RetroStack/TRS-80-Model-I-Jap20-E1/KiCAD/AddressDecoder.kicad_sch

## KiCad design KiCAD/AddressDecoder.kicad_sch (2025-06-16)

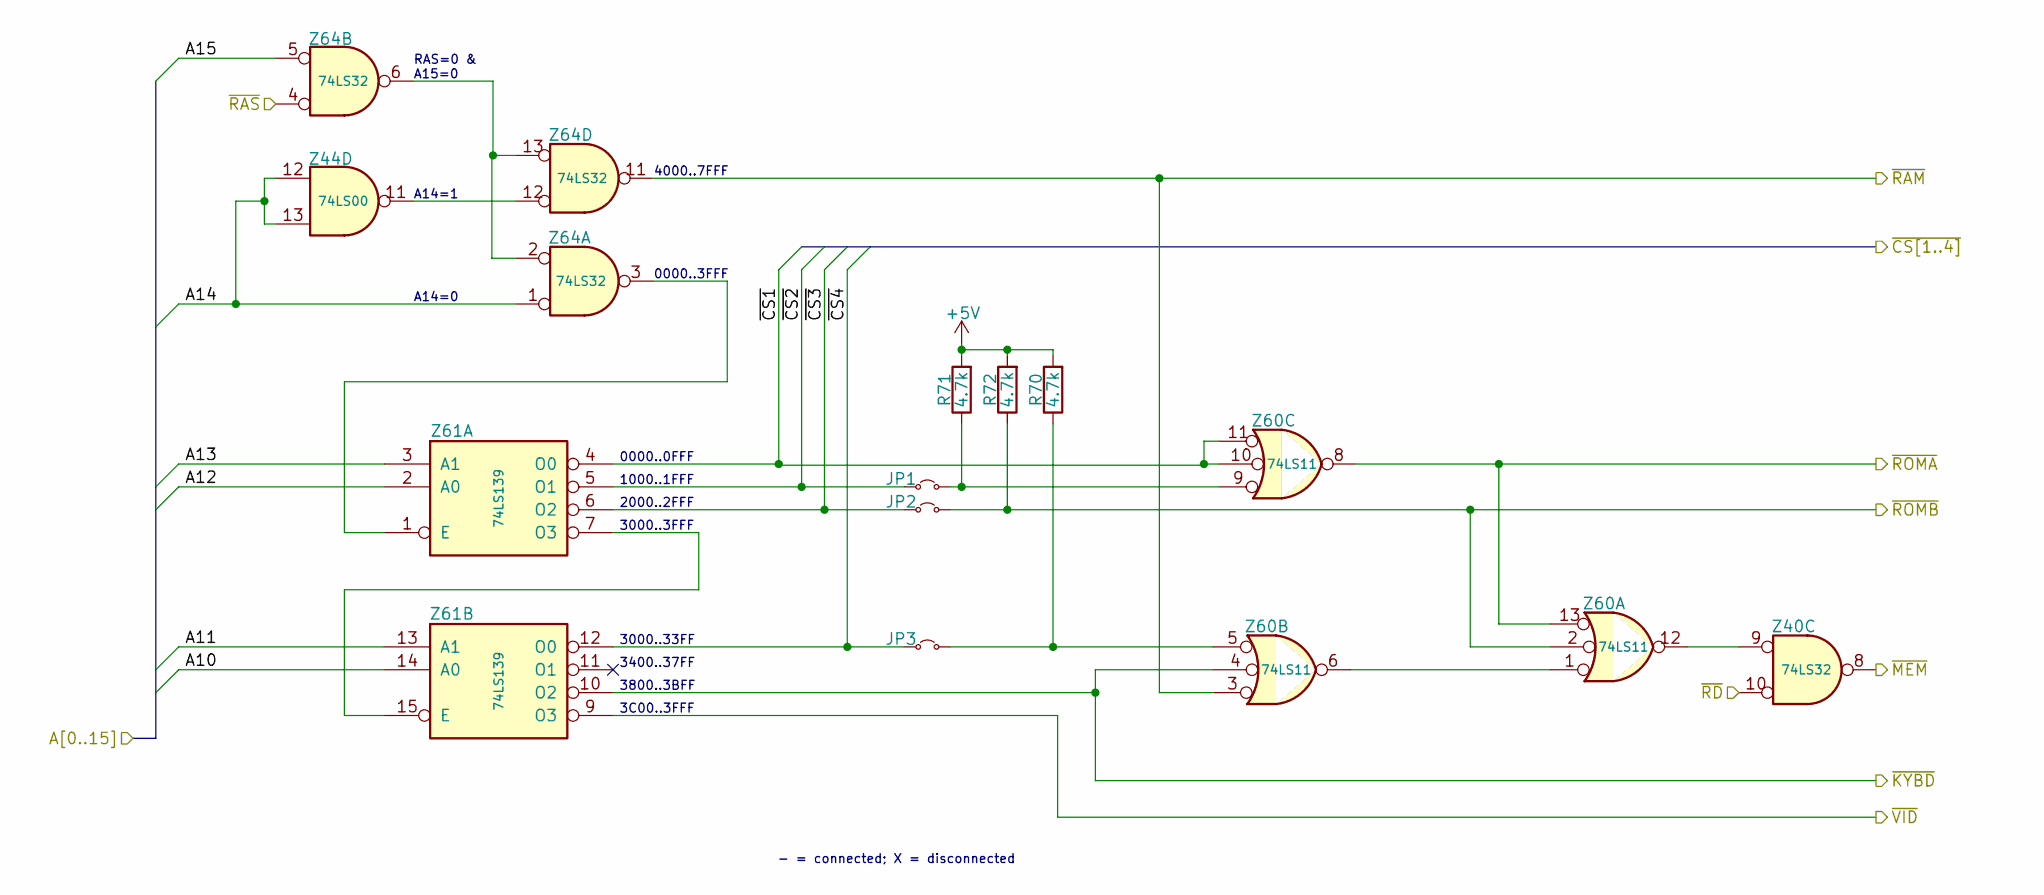
[picture p28: schematic AddressDecoder.kicad_sch]

Parts:
JP1, JP2, JP3: TRS80_Model_I_Jumper_2_Jap; TRS80_Model_I_Jumper_2_Open_Jap
R70, R71, R72: 4.7k; TRS80_Model_I_R_0.25W_Jap
Z40, Z64: 74LS32; TRS80_Model_I_DIP14_Jap
Z44: 74LS00; TRS80_Model_I_DIP14_Jap
Z60: 74LS11; TRS80_Model_I_DIP14_Jap
Z61: 74LS139; TRS80_Model_I_DIP16_Jap

Connections:
+5V: R70.2, R71.2, R72.2
A10: Z61.14 (A0)
A11: Z61.13 (A1)
A12: Z61.2 (A0)
A13: Z61.3 (A1)
A14: Z44.12, Z44.13, Z64.1
A15: Z64.5
unnamed: JP1.2 (B), R71.1, Z60.9
unnamed: JP3.2 (B), R70.1, Z60.5
unnamed: Z40.9, Z60.12
unnamed: Z44.11, Z64.12
unnamed: Z60.1, Z60.6
unnamed: Z61.1 (E), Z64.3
unnamed: Z61.7 (O3), Z61.15 (E)
unnamed: Z64.2, Z64.6, Z64.13
~CS1: Z60.10, Z60.11, Z61.4 (O0)
~CS2: JP1.1 (A), Z61.5 (O1)
~CS3: JP2.1 (A), Z61.6 (O2)
~CS4: JP3.1 (A), Z61.12 (O0)
~KYBD: Z60.4, Z61.10 (O2)
~MEM: Z40.8
~RAM: Z60.3, Z64.11
~RAS: Z64.4
~RD: Z40.10
~ROMA: Z60.8, Z60.13
~ROMB: JP2.2 (B), R72.1, Z60.2
~VID: Z61.9 (O3)

Notes on the sheet:
RAS=0 & A15=0
4000..7FFF
3000..33FF
0000..0FFF
- = connected; X = disconnected
A14=1
1000..1FFF
3000..3FFF
3800..3BFF
3C00..3FFF
A14=0
3400..37FF
2000..2FFF
0000..3FFF
