RetroStack/TRS-80-Model-I-Jap20-E1/KiCAD/CPU.kicad_sch

## KiCad design KiCAD/CPU.kicad_sch (2025-06-16)

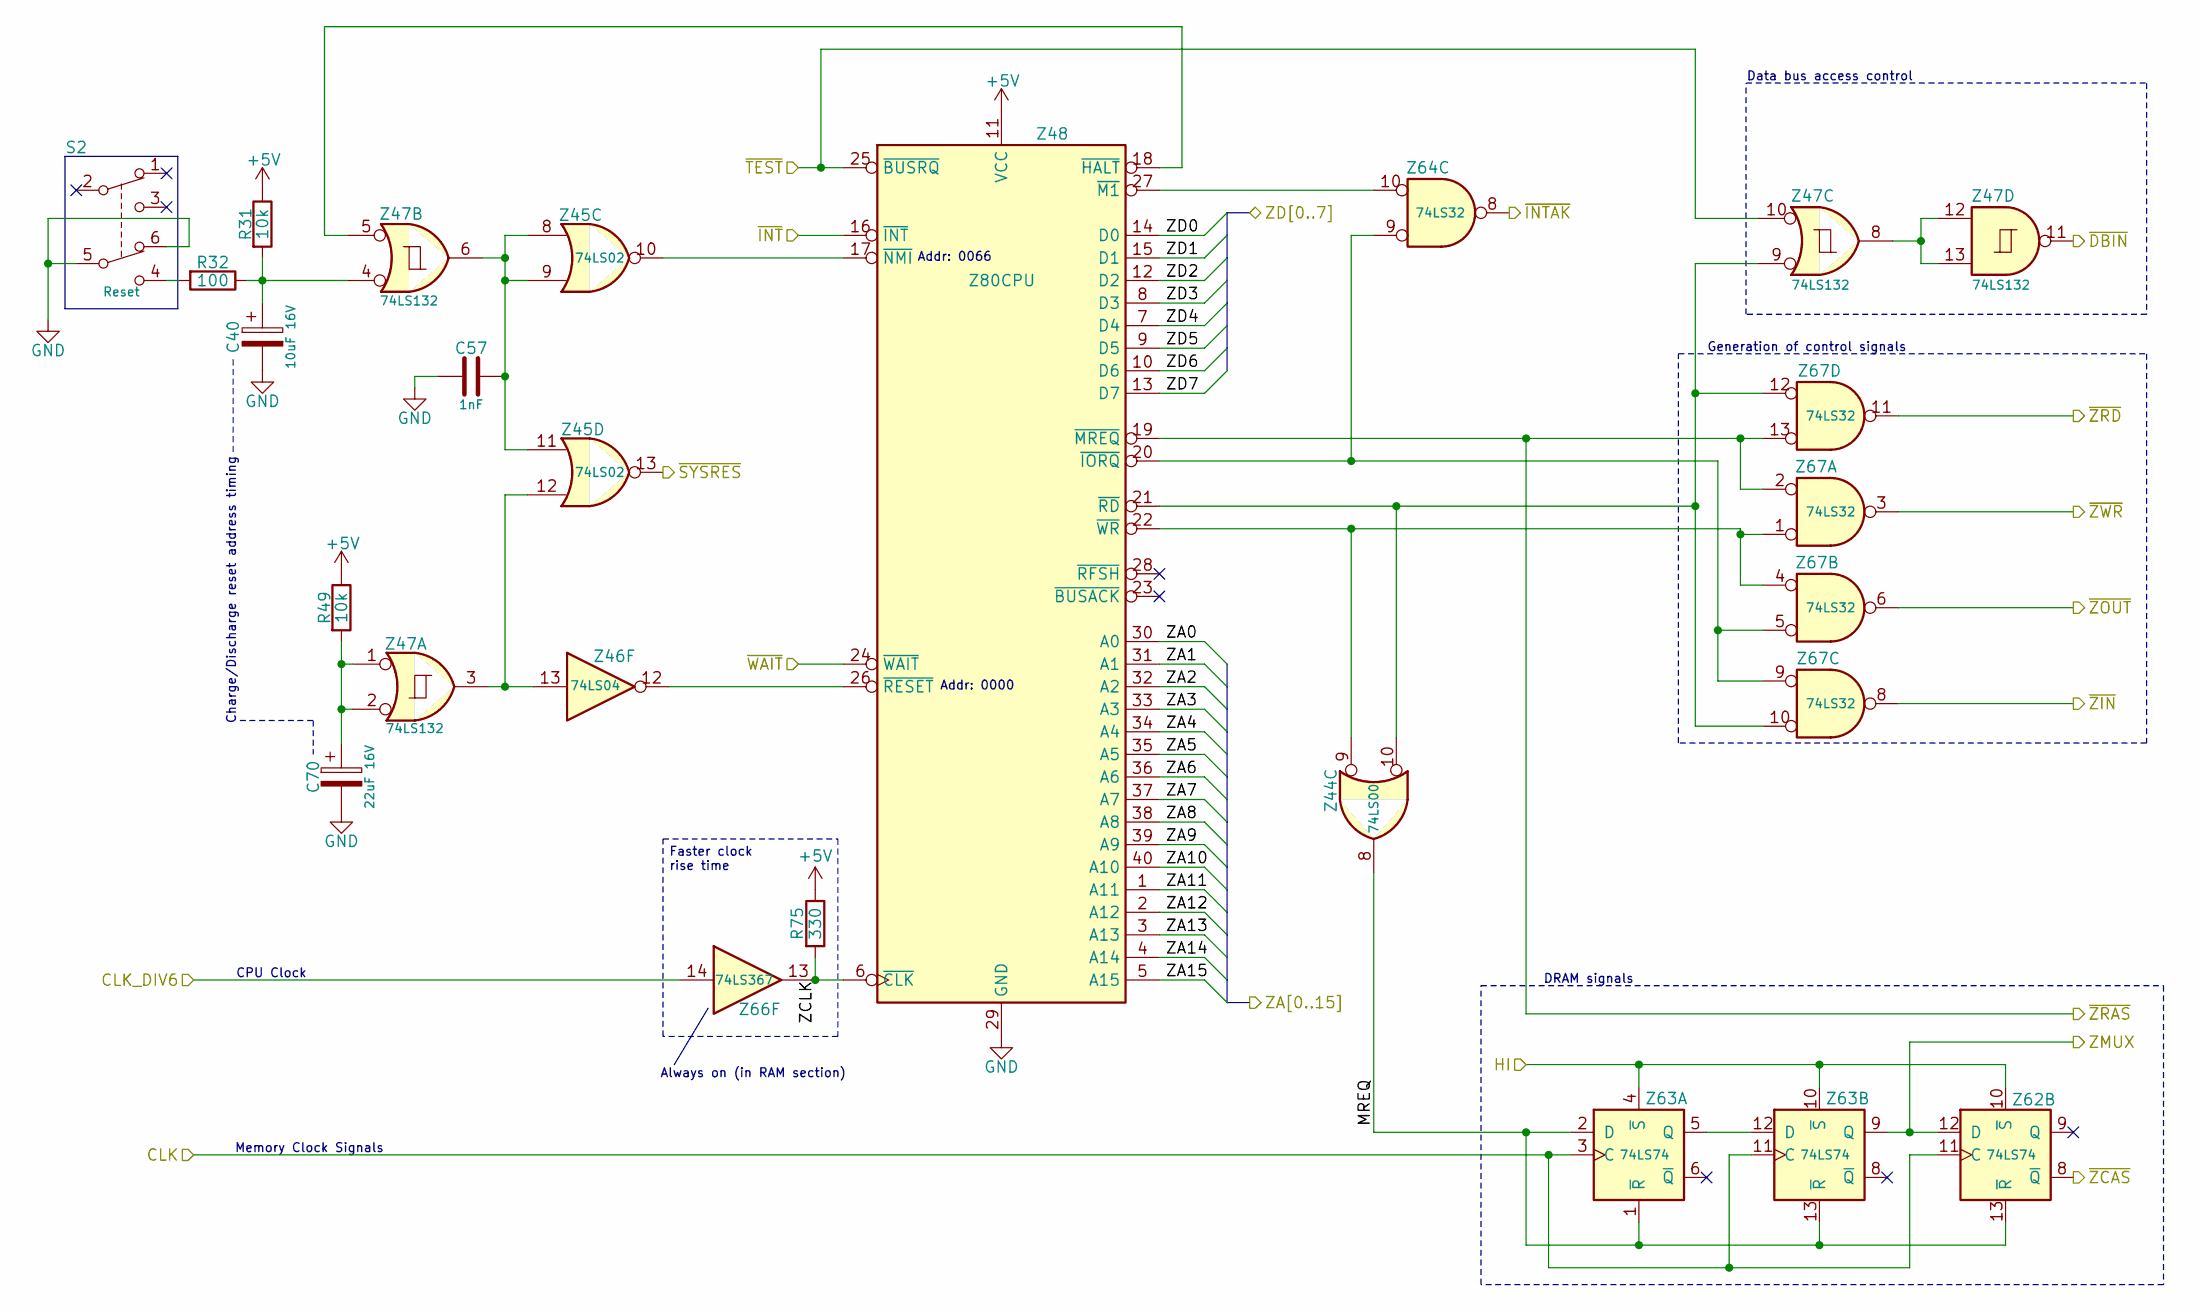
[picture p29: schematic CPU.kicad_sch]

Parts:
C40: 10uF 16V; TRS80_Model_I_C_Pol_Radial_5D_2.5P_Jap
C57: 1nF; TRS80_Model_I_C_Disc_9.5L_4W_6P_Small_Jap
C70: 22uF 16V; TRS80_Model_I_C_Pol_Radial_5D_2.5P_Jap
R31, R49: 10k; TRS80_Model_I_R_0.25W_Jap
R32: 100; TRS80_Model_I_R_0.25W_Jap
R75: 330; TRS80_Model_I_R_0.25W_Jap
S2: Reset; TRS80_Model_I_Sw_Small_Jap
Z44: 74LS00; TRS80_Model_I_DIP14_Jap
Z45: 74LS02; TRS80_Model_I_DIP14_Jap
Z46: 74LS04; TRS80_Model_I_DIP14_Jap
Z47: 74LS132; TRS80_Model_I_DIP14_Jap
Z48: Z80CPU; TRS80_Model_I_DIP40_Jap
Z62, Z63: 74LS74; TRS80_Model_I_DIP14_Jap
Z64, Z67: 74LS32; TRS80_Model_I_DIP14_Jap
Z66: 74LS367; TRS80_Model_I_DIP16_Jap

Connections:
+5V: R31.1, R49.1, R75.1, Z48.11 (VCC)
CLK: Z62.11 (C), Z63.3 (C), Z63.11 (C)
CLK_DIV6: Z66.14
GND: C40.2, C57.1, C70.2, S2.5, S2.6, Z48.29 (GND)
HI: Z62.10 (~S), Z63.4 (~S), Z63.10 (~S)
MREQ: Z44.8, Z62.13 (~R), Z63.1 (~R), Z63.2 (D), Z63.13 (~R)
unnamed: C40.1, R31.2, R32.1, Z47.4
unnamed: C57.2, Z45.8, Z45.9, Z45.11, Z47.6
unnamed: C70.1, R49.2, Z47.1, Z47.2
unnamed: R32.2, S2.4
unnamed: Z44.9, Z48.22 (~WR), Z67.1, Z67.4
unnamed: Z44.10, Z47.9, Z48.21 (~RD), Z67.10, Z67.12
unnamed: Z45.10, Z48.17 (~NMI)
unnamed: Z45.12, Z46.13, Z47.3
unnamed: Z46.12, Z48.26 (~RESET)
unnamed: Z47.5, Z48.18 (~HALT)
unnamed: Z47.8, Z47.12, Z47.13
unnamed: Z48.20 (~IORQ), Z64.9, Z67.5, Z67.9
unnamed: Z48.27 (~M1), Z64.10
unnamed: Z63.5 (Q), Z63.12 (D)
ZA0: Z48.30 (A0)
ZA1: Z48.31 (A1)
ZA2: Z48.32 (A2)
ZA3: Z48.33 (A3)
ZA4: Z48.34 (A4)
ZA5: Z48.35 (A5)
ZA6: Z48.36 (A6)
ZA7: Z48.37 (A7)
ZA8: Z48.38 (A8)
ZA9: Z48.39 (A9)
ZA10: Z48.40 (A10)
ZA11: Z48.1 (A11)
ZA12: Z48.2 (A12)
ZA13: Z48.3 (A13)
ZA14: Z48.4 (A14)
ZA15: Z48.5 (A15)
ZCLK: R75.2, Z48.6 (~CLK), Z66.13
ZD0: Z48.14 (D0)
ZD1: Z48.15 (D1)
ZD2: Z48.12 (D2)
ZD3: Z48.8 (D3)
ZD4: Z48.7 (D4)
ZD5: Z48.9 (D5)
ZD6: Z48.10 (D6)
ZD7: Z48.13 (D7)
ZMUX: Z62.12 (D), Z63.9 (Q)
~DBIN: Z47.11
~INTAK: Z64.8
~INT: Z48.16 (~INT)
~SYSRES: Z45.13
~TEST: Z47.10, Z48.25 (~BUSRQ)
~WAIT: Z48.24 (~WAIT)
~ZCAS: Z62.8 (~Q)
~ZIN: Z67.8
~ZOUT: Z67.6
~ZRAS: Z48.19 (~MREQ), Z67.2, Z67.13
~ZRD: Z67.11
~ZWR: Z67.3

Notes on the sheet:
CPU Clock
Always on (in RAM section)
Data bus access control
Generation of control signals
DRAM signals
Faster clock rise time
Memory Clock Signals
Addr: 0000
Charge/Discharge reset address timing
Addr: 0066
