RetroStack/TRS-80-Model-I-Jap20-E1/KiCAD/CPUGating.kicad_sch

## KiCad design KiCAD/CPUGating.kicad_sch (2025-06-16)

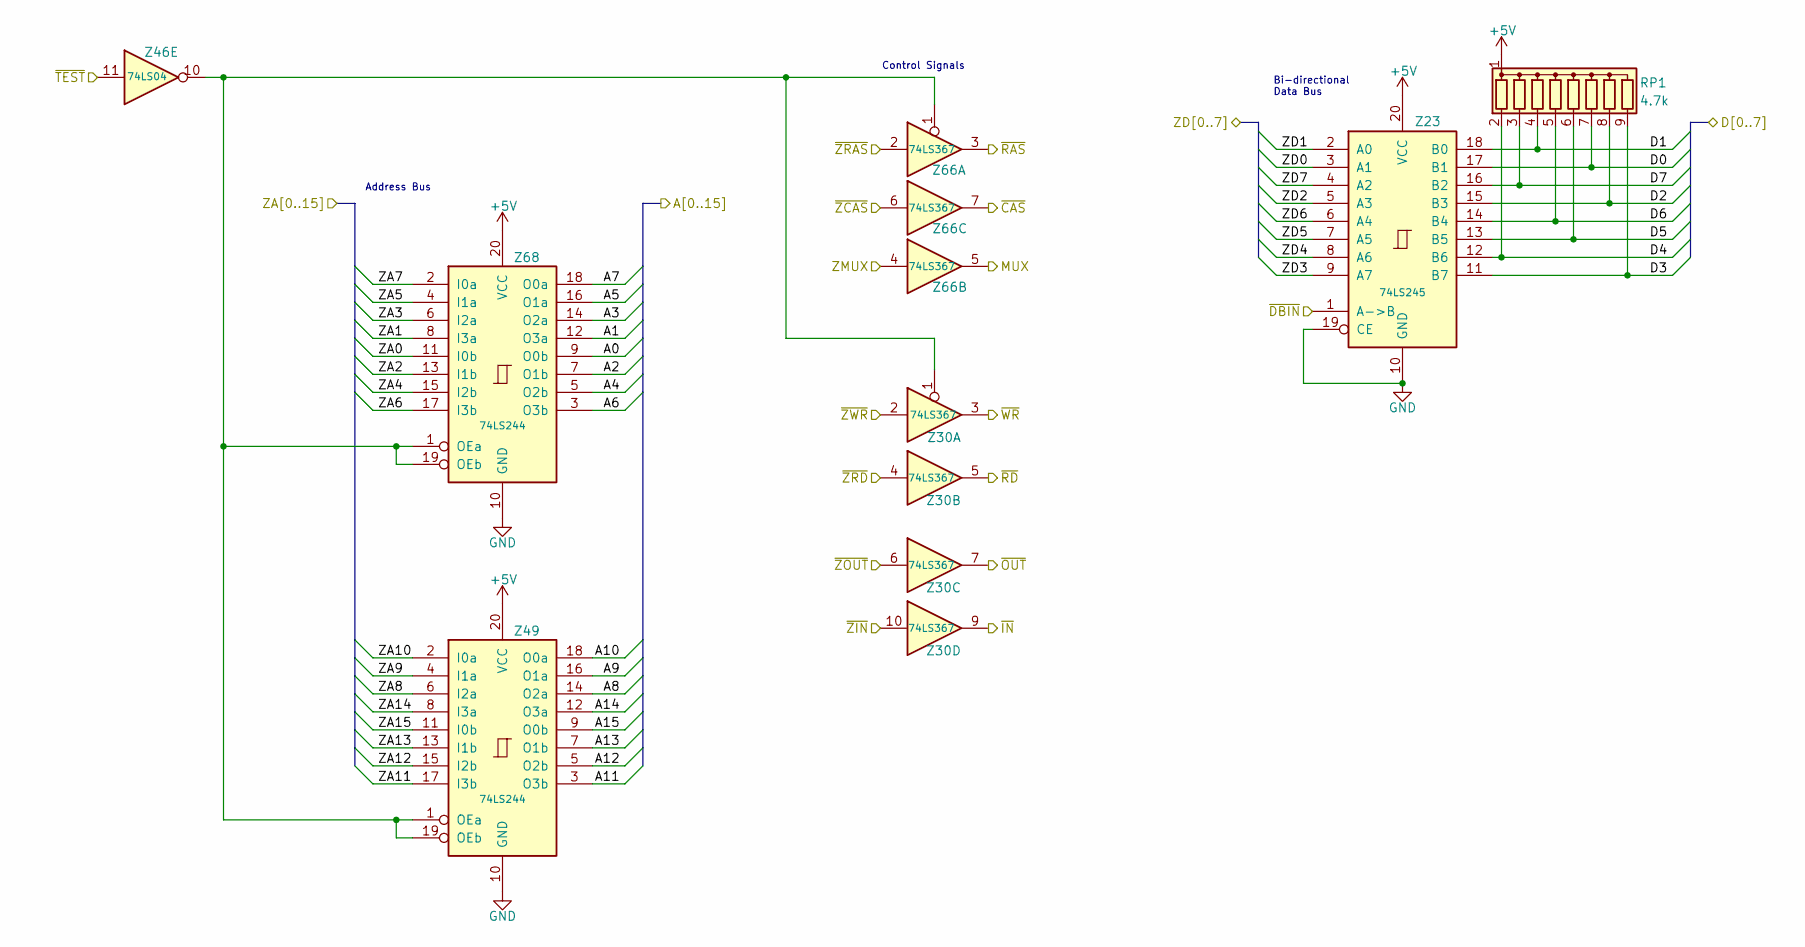
[picture p30: schematic CPUGating.kicad_sch]

Parts:
RP1: 4.7k; TRS80_Model_I_R_Array_09_Jap
Z23: 74LS245; TRS80_Model_I_DIP20_Jap
Z30, Z66: 74LS367; TRS80_Model_I_DIP16_Jap
Z46: 74LS04; TRS80_Model_I_DIP14_Jap
Z49, Z68: 74LS244; TRS80_Model_I_DIP20_Jap

Connections:
+5V: RP1.1 (common), Z23.20 (VCC), Z49.20 (VCC), Z68.20 (VCC)
A0: Z68.9 (O0b)
A1: Z68.12 (O3a)
A2: Z68.7 (O1b)
A3: Z68.14 (O2a)
A4: Z68.5 (O2b)
A5: Z68.16 (O1a)
A6: Z68.3 (O3b)
A7: Z68.18 (O0a)
A8: Z49.14 (O2a)
A9: Z49.16 (O1a)
A10: Z49.18 (O0a)
A11: Z49.3 (O3b)
A12: Z49.5 (O2b)
A13: Z49.7 (O1b)
A14: Z49.12 (O3a)
A15: Z49.9 (O0b)
D0: RP1.7 (R6), Z23.17 (B1)
D1: RP1.4 (R3), Z23.18 (B0)
D2: RP1.8 (R7), Z23.15 (B3)
D3: RP1.9 (R8), Z23.11 (B7)
D4: RP1.2 (R1), Z23.12 (B6)
D5: RP1.6 (R5), Z23.13 (B5)
D6: RP1.5 (R4), Z23.14 (B4)
D7: RP1.3 (R2), Z23.16 (B2)
GND: Z23.10 (GND), Z23.19 (CE), Z49.10 (GND), Z68.10 (GND)
MUX: Z66.5
unnamed: Z30.1, Z46.10, Z49.1 (OEa), Z49.19 (OEb), Z66.1, Z68.1 (OEa), Z68.19 (OEb)
ZA0: Z68.11 (I0b)
ZA1: Z68.8 (I3a)
ZA2: Z68.13 (I1b)
ZA3: Z68.6 (I2a)
ZA4: Z68.15 (I2b)
ZA5: Z68.4 (I1a)
ZA6: Z68.17 (I3b)
ZA7: Z68.2 (I0a)
ZA8: Z49.6 (I2a)
ZA9: Z49.4 (I1a)
ZA10: Z49.2 (I0a)
ZA11: Z49.17 (I3b)
ZA12: Z49.15 (I2b)
ZA13: Z49.13 (I1b)
ZA14: Z49.8 (I3a)
ZA15: Z49.11 (I0b)
ZD0: Z23.3 (A1)
ZD1: Z23.2 (A0)
ZD2: Z23.5 (A3)
ZD3: Z23.9 (A7)
ZD4: Z23.8 (A6)
ZD5: Z23.7 (A5)
ZD6: Z23.6 (A4)
ZD7: Z23.4 (A2)
ZMUX: Z66.4
~CAS: Z66.7
~DBIN: Z23.1 (A->B)
~IN: Z30.9
~OUT: Z30.7
~RAS: Z66.3
~RD: Z30.5
~TEST: Z46.11
~WR: Z30.3
~ZCAS: Z66.6
~ZIN: Z30.10
~ZOUT: Z30.6
~ZRAS: Z66.2
~ZRD: Z30.4
~ZWR: Z30.2

Notes on the sheet:
Bi-directional Data Bus
Address Bus
Control Signals
