RetroStack/TRS-80-Model-I-Jap20-E1/KiCAD/Capacitors.kicad_sch

## KiCad design KiCAD/Capacitors.kicad_sch (2025-06-16)

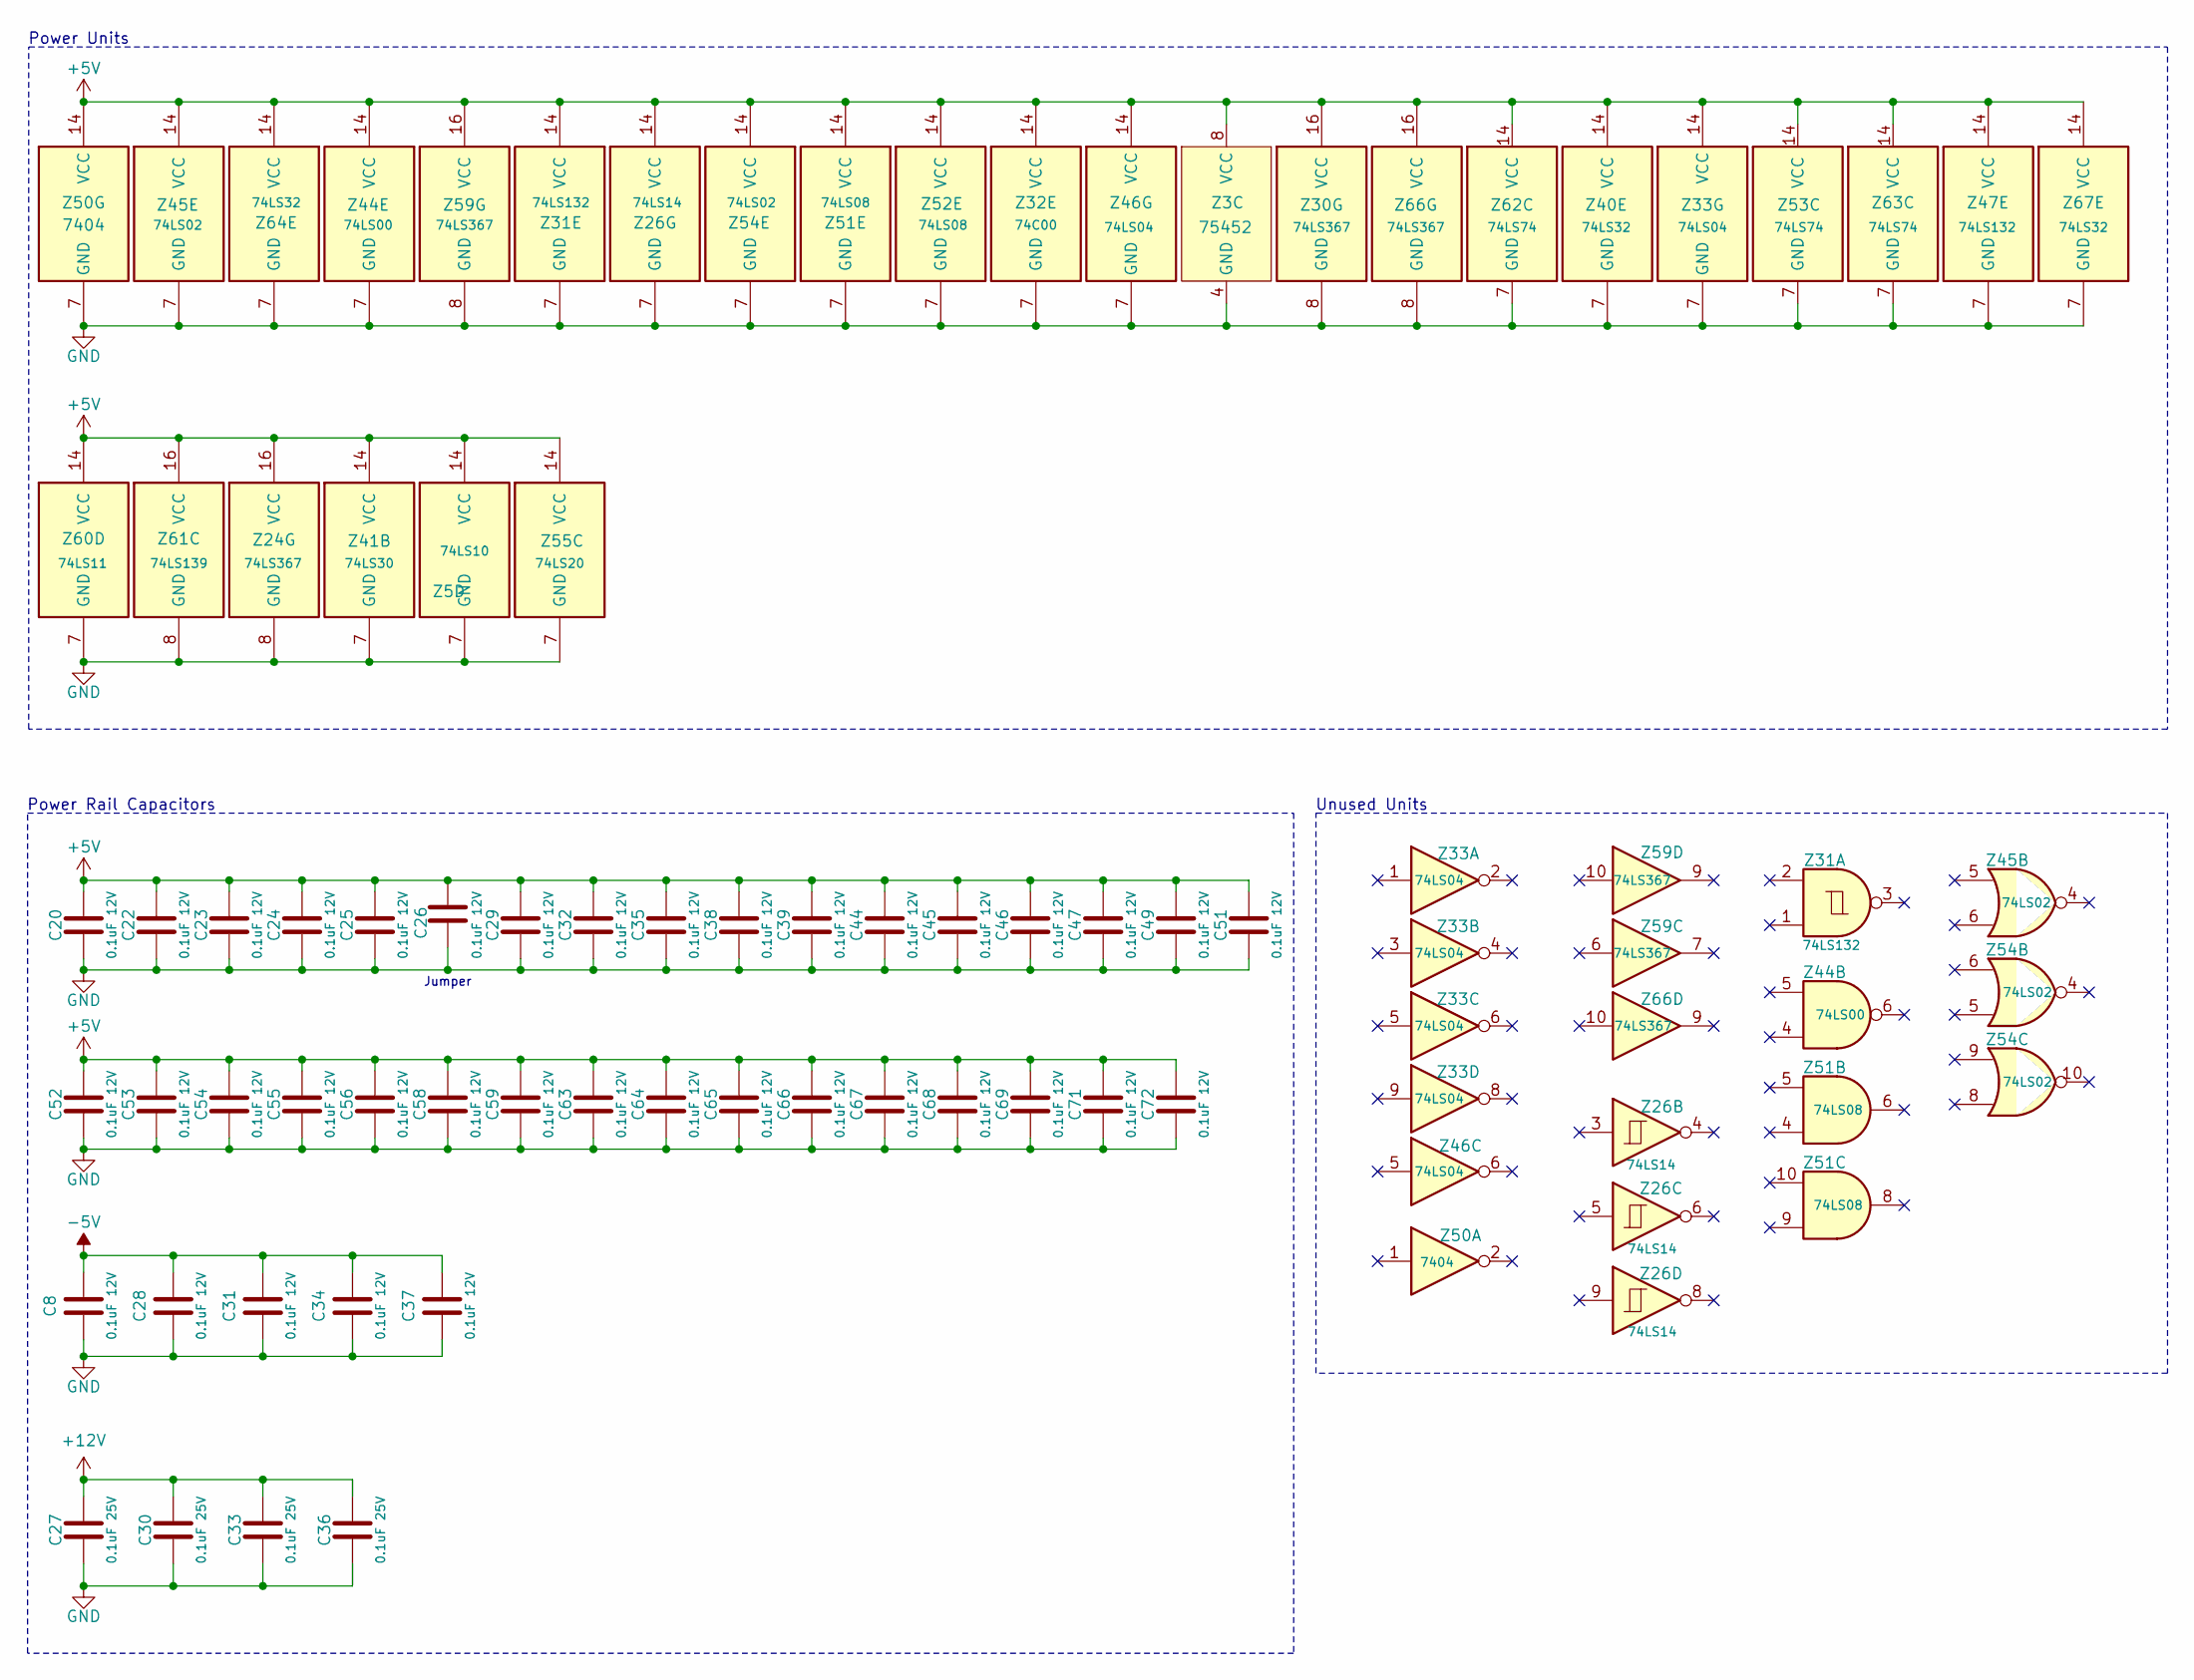
[picture p31: schematic Capacitors.kicad_sch]

Parts:
C8, C20, C22, C23, C24, C25, C26, C28, C29, C31, C32, C34, C35, C37, C38, C39, C44, C45, C46, C47, C49, C51, C52, C53, C54, C55, C56, C58, C59, C63, C64, C65, C66, C67, C68, C69, C71, C72: 0.1uF 12V; TRS80_Model_I_C_Disc_9.5L_4W_6P_Jap
C27, C30, C33, C36: 0.1uF 25V; TRS80_Model_I_C_Disc_9.5L_4W_6P_Jap
Z3: 75452; TRS80_Model_I_DIP8_Jap
Z5: 74LS10; TRS80_Model_I_DIP14_Jap
Z24, Z30, Z59, Z66: 74LS367; TRS80_Model_I_DIP16_Jap
Z26: 74LS14; TRS80_Model_I_DIP14_Jap
Z31, Z47: 74LS132; TRS80_Model_I_DIP14_Jap
Z32: 74C00; TRS80_Model_I_DIP14_Jap
Z33, Z46: 74LS04; TRS80_Model_I_DIP14_Jap
Z40, Z64, Z67: 74LS32; TRS80_Model_I_DIP14_Jap
Z41: 74LS30; TRS80_Model_I_DIP14_Jap
Z44: 74LS00; TRS80_Model_I_DIP14_Jap
Z45, Z54: 74LS02; TRS80_Model_I_DIP14_Jap
Z50: 7404; TRS80_Model_I_DIP14_Jap
Z51, Z52: 74LS08; TRS80_Model_I_DIP14_Jap
Z53, Z62, Z63: 74LS74; TRS80_Model_I_DIP14_Jap
Z55: 74LS20; TRS80_Model_I_DIP14_Jap
Z60: 74LS11; TRS80_Model_I_DIP14_Jap
Z61: 74LS139; TRS80_Model_I_DIP16_Jap

Connections:
+5V: C20.1, C22.1, C23.1, C24.1, C25.1, C26.1, C29.1, C32.1, C35.1, C38.1, C39.1, C44.1, C45.1, C46.1, C47.1, C49.1, C51.1, C52.1, C53.1, C54.1, C55.1, C56.1, C58.1, C59.1, C63.1, C64.1, C65.1, C66.1, C67.1, C68.1, C69.1, C71.1, C72.1, Z3.8 (VCC), Z5.14 (VCC), Z24.16 (VCC), Z26.14 (VCC), Z30.16 (VCC), Z31.14 (VCC), Z32.14 (VCC), Z33.14 (VCC), Z40.14 (VCC), Z41.14 (VCC), Z44.14 (VCC), Z45.14 (VCC), Z46.14 (VCC), Z47.14 (VCC), Z50.14 (VCC), Z51.14 (VCC), Z52.14 (VCC), Z53.14 (VCC), Z54.14 (VCC), Z55.14 (VCC), Z59.16 (VCC), Z60.14 (VCC), Z61.16 (VCC), Z62.14 (VCC), Z63.14 (VCC), Z64.14 (VCC), Z66.16 (VCC), Z67.14 (VCC)
+12V: C27.1, C30.1, C33.1, C36.1
-5V: C8.1, C28.1, C31.1, C34.1, C37.1
GND: C8.2, C20.2, C22.2, C23.2, C24.2, C25.2, C26.2, C27.2, C28.2, C29.2, C30.2, C31.2, C32.2, C33.2, C34.2, C35.2, C36.2, C37.2, C38.2, C39.2, C44.2, C45.2, C46.2, C47.2, C49.2, C51.2, C52.2, C53.2, C54.2, C55.2, C56.2, C58.2, C59.2, C63.2, C64.2, C65.2, C66.2, C67.2, C68.2, C69.2, C71.2, C72.2, Z3.4 (GND), Z5.7 (GND), Z24.8 (GND), Z26.7 (GND), Z30.8 (GND), Z31.7 (GND), Z32.7 (GND), Z33.7 (GND), Z40.7 (GND), Z41.7 (GND), Z44.7 (GND), Z45.7 (GND), Z46.7 (GND), Z47.7 (GND), Z50.7 (GND), Z51.7 (GND), Z52.7 (GND), Z53.7 (GND), Z54.7 (GND), Z55.7 (GND), Z59.8 (GND), Z60.7 (GND), Z61.8 (GND), Z62.7 (GND), Z63.7 (GND), Z64.7 (GND), Z66.8 (GND), Z67.7 (GND)

Notes on the sheet:
Power Units
Unused Units
Power Rail Capacitors
Jumper
