RetroStack/TRS-80-Model-I-Jap20-E1/KiCAD/CardEdgeInterface.kicad_sch

## KiCad design KiCAD/CardEdgeInterface.kicad_sch (2025-06-16)

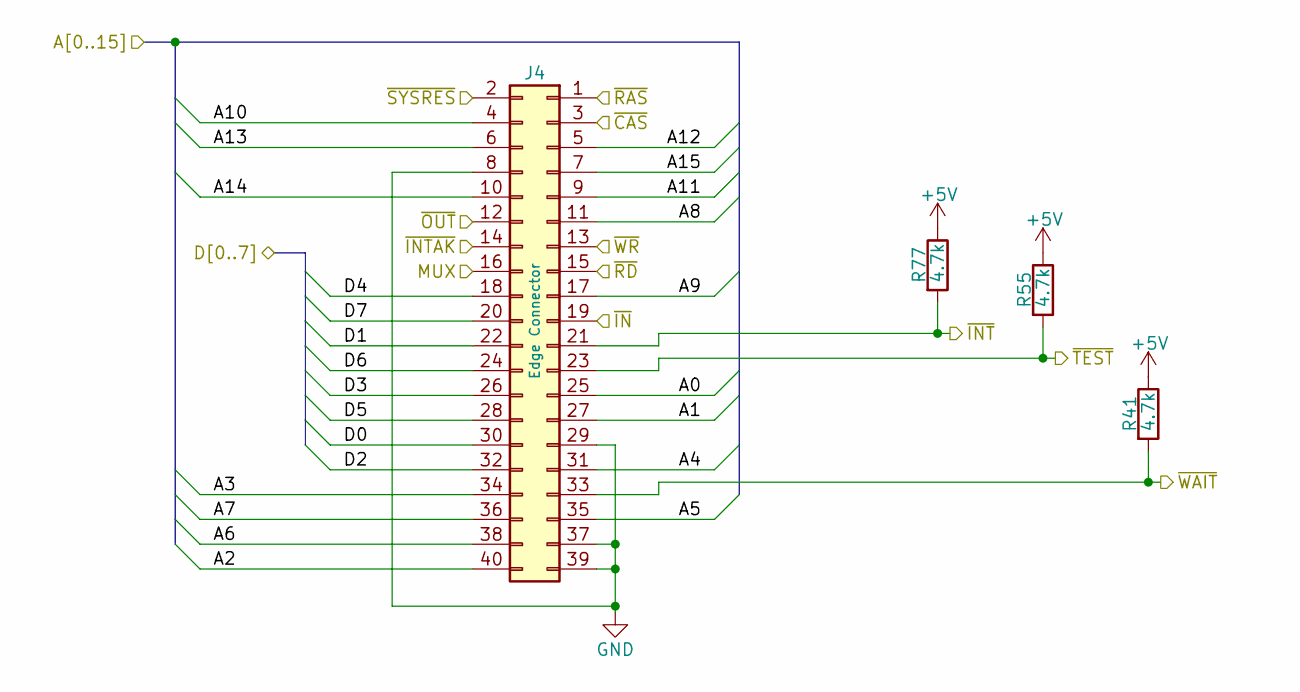
[picture p32: schematic CardEdgeInterface.kicad_sch]

Parts:
J4: Edge Connector; TRS80_Model_I_Edge_Connector_Jap
R41, R55, R77: 4.7k; TRS80_Model_I_R_0.25W_Jap

Connections:
+5V: R41.1, R55.1, R77.1
A0: J4.25
A1: J4.27
A2: J4.40
A3: J4.34
A4: J4.31
A5: J4.35
A6: J4.38
A7: J4.36
A8: J4.11
A9: J4.17
A10: J4.4
A11: J4.9
A12: J4.5
A13: J4.6
A14: J4.10
A15: J4.7
D0: J4.30
D1: J4.22
D2: J4.32
D3: J4.26
D4: J4.18
D5: J4.28
D6: J4.24
D7: J4.20
GND: J4.8, J4.29, J4.37, J4.39
MUX: J4.16
~CAS: J4.3
~INTAK: J4.14
~INT: J4.21, R77.2
~IN: J4.19
~OUT: J4.12
~RAS: J4.1
~RD: J4.15
~SYSRES: J4.2
~TEST: J4.23, R55.2
~WAIT: J4.33, R41.2
~WR: J4.13
