RetroStack/TRS-80-Model-I-Jap20-E1/KiCAD/Cassette.kicad_sch

## KiCad design KiCAD/Cassette.kicad_sch (2025-06-16)

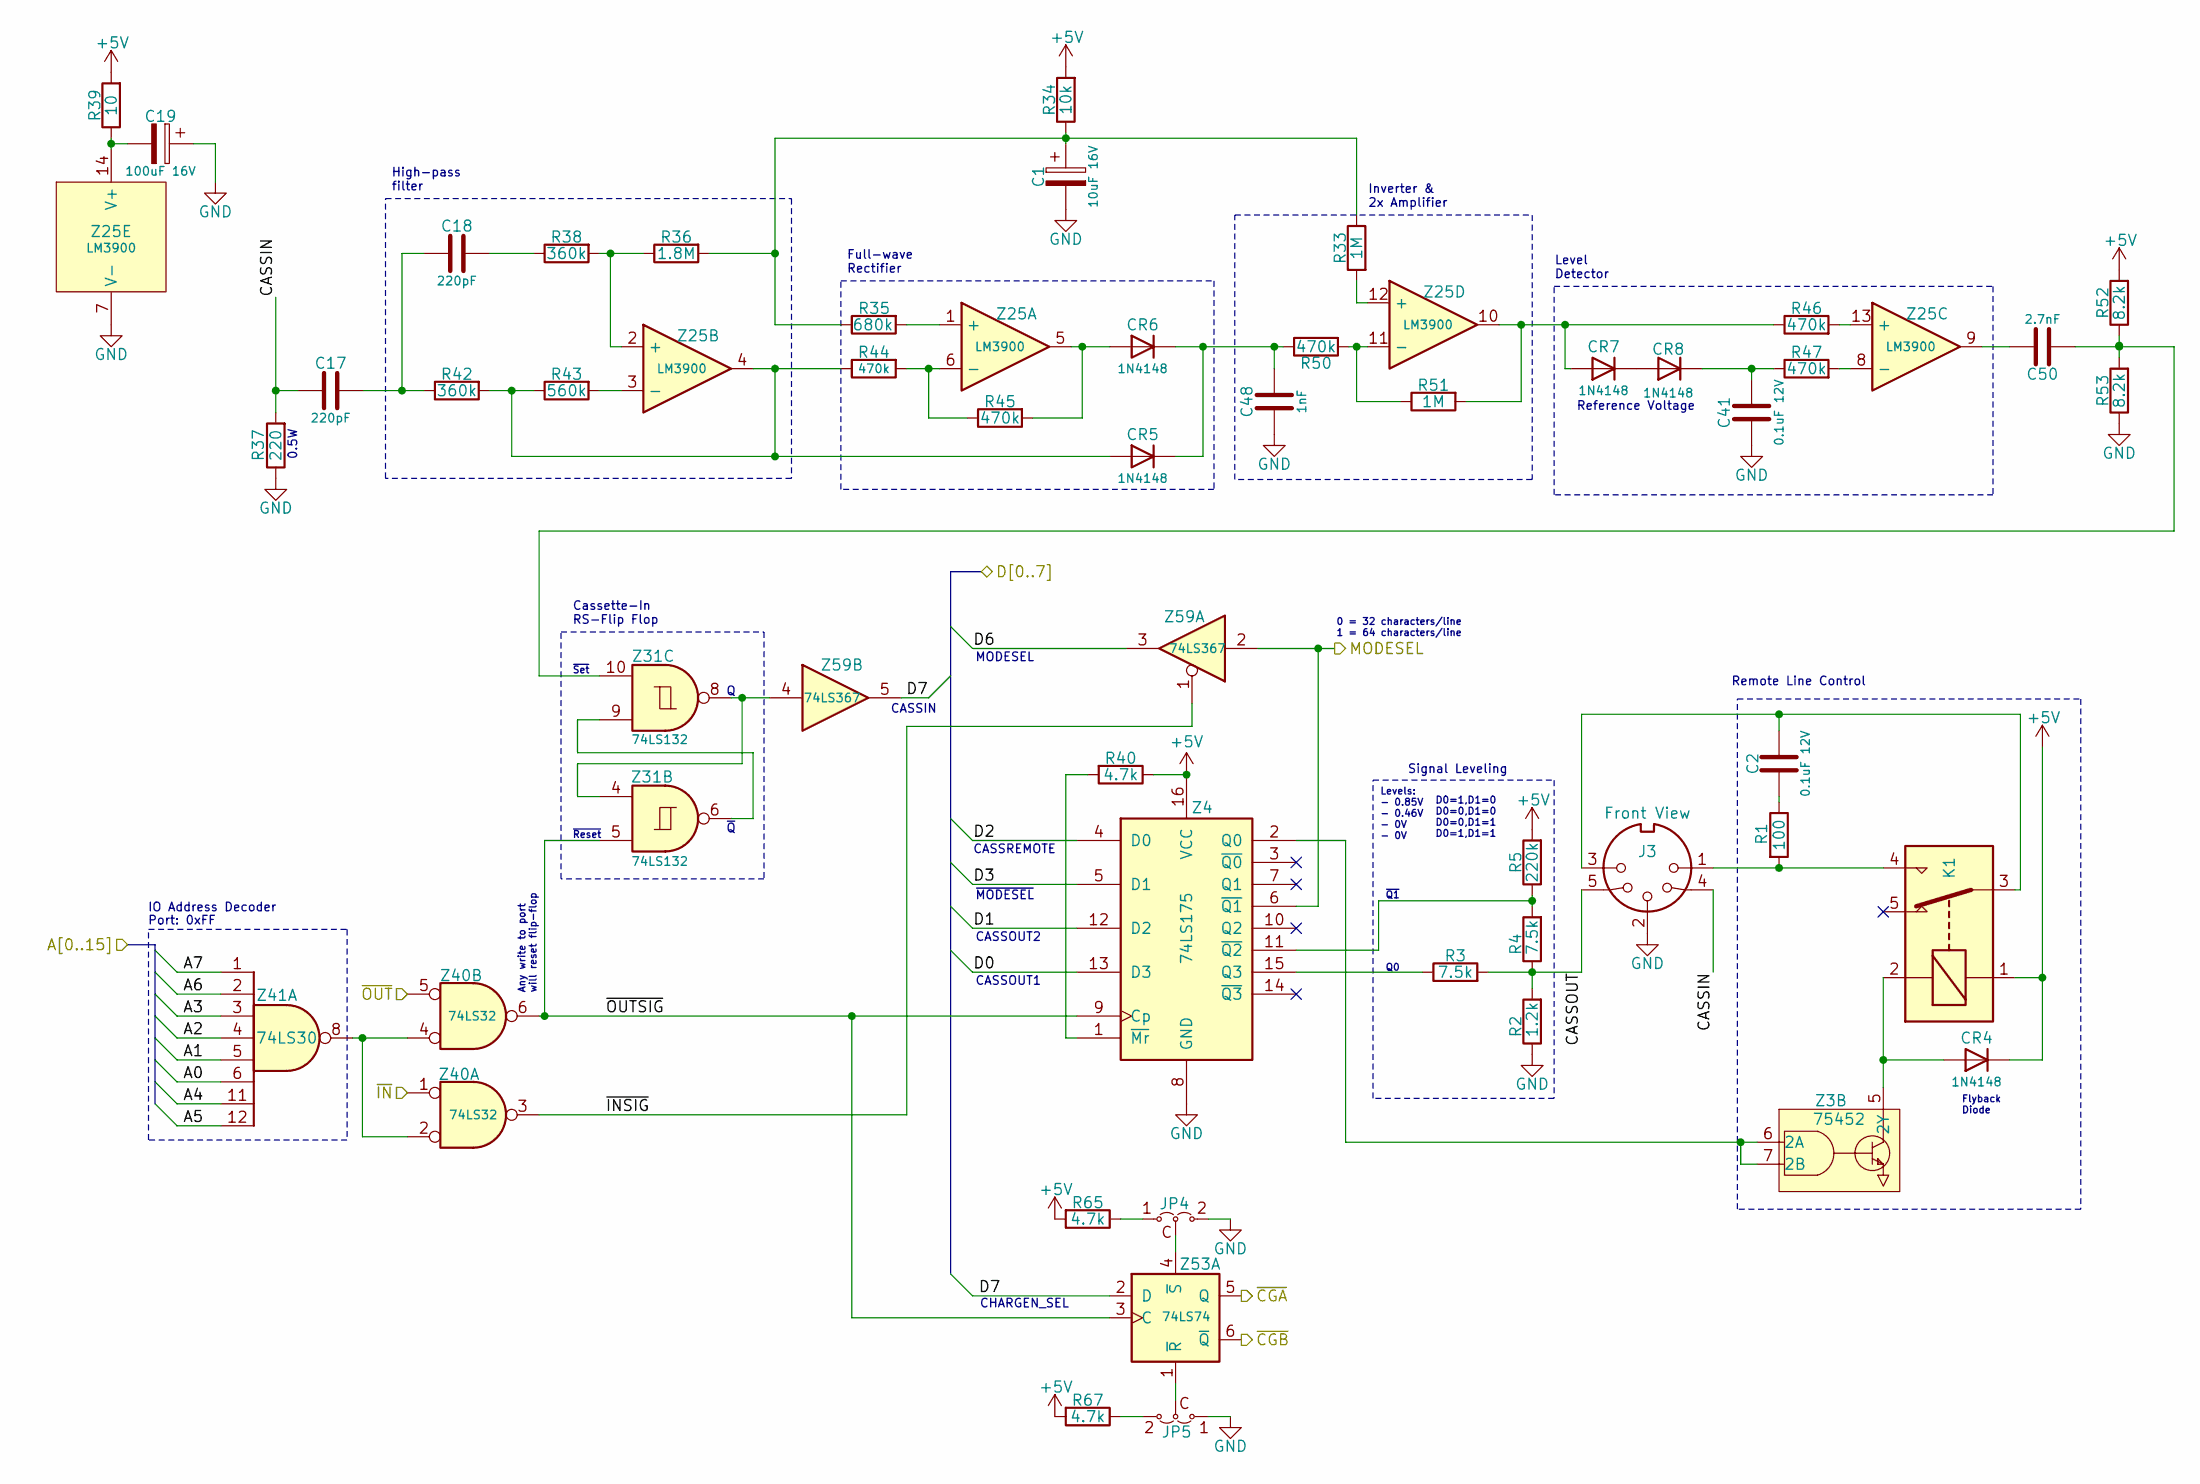
[picture p33: schematic Cassette.kicad_sch]

Parts:
C1: 10uF 16V; TRS80_Model_I_C_Pol_Radial_5D_2.5P_Jap
C2, C41: 0.1uF 12V; TRS80_Model_I_C_Disc_9.5L_4W_6P_Jap
C17, C18: 220pF; TRS80_Model_I_C_Disc_9.5L_4W_6P_Jap
C19: 100uF 16V; TRS80_Model_I_C_Pol_Radial_10D_5P_Jap
C48: 1nF; TRS80_Model_I_C_Disc_9.5L_4W_6P_Jap
C50: 2.7nF; TRS80_Model_I_C_Disc_9.5L_4W_6P_Jap
CR4, CR5, CR6, CR7, CR8: 1N4148; TRS80_Model_I_D_Jap
J3: Front View; TRS80_Model_I_DIN5_Jap
JP4: TRS80_Model_I_Jumper_3_Jap; TRS80_Model_I_Jumper_3_Open_Jap
JP5: TRS80_Model_I_Jumper_3_Jap; TRS80_Model_I_Jumper_3_Open_HFlipped_Jap
K1: Relay_SPDT; TRS80_Model_I_Relay_Jap
R1: 100; TRS80_Model_I_R_0.25W_Jap
R2: 1.2k; TRS80_Model_I_R_0.25W_Jap
R3, R4: 7.5k; TRS80_Model_I_R_0.25W_Jap
R5: 220k; TRS80_Model_I_R_0.25W_Jap
R33, R51: 1M; TRS80_Model_I_R_0.25W_Jap
R34: 10k; TRS80_Model_I_R_0.25W_Jap
R35: 680k; TRS80_Model_I_R_0.25W_Jap
R36: 1.8M; TRS80_Model_I_R_0.25W_Jap
R37: 220; TRS80_Model_I_R_0.5W_Jap
R38, R42: 360k; TRS80_Model_I_R_0.25W_Jap
R39: 10; TRS80_Model_I_R_0.25W_Jap
R40, R65, R67: 4.7k; TRS80_Model_I_R_0.25W_Jap
R43: 560k; TRS80_Model_I_R_0.25W_Jap
R44, R45, R46, R47, R50: 470k; TRS80_Model_I_R_0.25W_Jap
R52, R53: 8.2k; TRS80_Model_I_R_0.25W_Jap
Z3: 75452; TRS80_Model_I_DIP8_Jap
Z4: 74LS175; TRS80_Model_I_DIP16_Jap
Z25: LM3900; TRS80_Model_I_DIP14_Jap
Z31: 74LS132; TRS80_Model_I_DIP14_Jap
Z40: 74LS32; TRS80_Model_I_DIP14_Jap
Z41: 74LS30; TRS80_Model_I_DIP14_Jap
Z53: 74LS74; TRS80_Model_I_DIP14_Jap
Z59: 74LS367; TRS80_Model_I_DIP16_Jap

Connections:
+5V: CR4.1 (K), K1.1, R5.2, R34.2, R39.2, R40.1, R52.2, R65.2, R67.2, Z4.16 (VCC)
A0: Z41.6
A1: Z41.5
A2: Z41.4
A3: Z41.3
A4: Z41.11
A5: Z41.12
A6: Z41.2
A7: Z41.1
CASSIN: C17.1, J3.4, R37.2
CASSOUT: J3.5, R2.2, R3.2, R4.1
D0: Z4.13 (D3)
D1: Z4.12 (D2)
D2: Z4.4 (D0)
D3: Z4.5 (D1)
D6: Z59.3
D7: Z53.2 (D), Z59.5
GND: C1.2, C19.1, C41.1, C48.1, J3.2, JP4.3 (A), JP5.1 (A), R2.1, R37.1, R53.1, Z4.8 (GND), Z25.7 (V-)
MODESEL: Z4.6 (~Q1), Z59.2
unnamed: C1.1, R33.1, R34.1, R35.1, R36.2
unnamed: C2.1, R1.1
unnamed: C2.2, J3.3, K1.3
unnamed: C17.2, C18.1, R42.1
unnamed: C18.2, R38.1
unnamed: C19.2, R39.1, Z25.14 (V+)
unnamed: C41.2, CR8.1 (K), R47.1
unnamed: C48.2, CR5.1 (K), CR6.1 (K), R50.1
unnamed: C50.1, R52.1, R53.2, Z31.10
unnamed: C50.2, Z25.9
unnamed: CR4.2 (A), K1.2, Z3.5 (2Y)
unnamed: CR5.2 (A), R42.2, R43.1, R44.1, Z25.4
unnamed: CR6.2 (A), R45.2, Z25.5
unnamed: CR7.1 (K), CR8.2 (A)
unnamed: CR7.2 (A), R46.1, R51.2, Z25.10
unnamed: J3.1, K1.4, R1.2
unnamed: JP4.1 (A), R65.1
unnamed: JP4.2 (B), Z53.4 (~S)
unnamed: JP5.2 (B), Z53.1 (~R)
unnamed: JP5.3 (A), R67.1
unnamed: R3.1, Z4.15 (Q3)
unnamed: R4.2, R5.1, Z4.11 (~Q2)
unnamed: R33.2, Z25.12 (+)
unnamed: R35.2, Z25.1 (+)
unnamed: R36.1, R38.2, Z25.2 (+)
unnamed: R40.2, Z4.1 (~Mr)
unnamed: R43.2, Z25.3 (-)
unnamed: R44.2, R45.1, Z25.6 (-)
unnamed: R46.2, Z25.13 (+)
unnamed: R47.2, Z25.8 (-)
unnamed: R50.2, R51.1, Z25.11 (-)
unnamed: Z3.6 (2A), Z3.7 (2B), Z4.2 (Q0)
unnamed: Z31.4, Z31.8, Z59.4
unnamed: Z31.6, Z31.9
unnamed: Z40.2, Z40.4, Z41.8
~CGA: Z53.5 (Q)
~CGB: Z53.6 (~Q)
~INSIG: Z40.3, Z59.1
~IN: Z40.1
~OUTSIG: Z4.9 (Cp), Z31.5, Z40.6, Z53.3 (C)
~OUT: Z40.5

Notes on the sheet:
0 = 32 characters/line 1 = 64 characters/line
Full-wave Rectifier
Level Detector
~{Q1}
CHARGEN_SEL
High-pass filter
Reference Voltage
Any write to port will reset flip-flop
IO Address Decoder
Port: 0xFF
Signal Leveling
~{MODESEL}
~{Q}
CASSREMOTE
0.5W
Levels: - 0.85V - 0.46V - 0V - 0V
CASSIN
MODESEL
Cassette-In RS-Flip Flop
CASSOUT2
Remote Line Control
Inverter & 2x Amplifier
CASSOUT1
~{Reset}
~{Set}
D0=1,D1=0 D0=0,D1=0 D0=0,D1=1 D0=1,D1=1
Flyback Diode
