RetroStack/TRS-80-Model-I-Jap20-E1/KiCAD/Clock.kicad_sch

## KiCad design KiCAD/Clock.kicad_sch (2025-06-16)

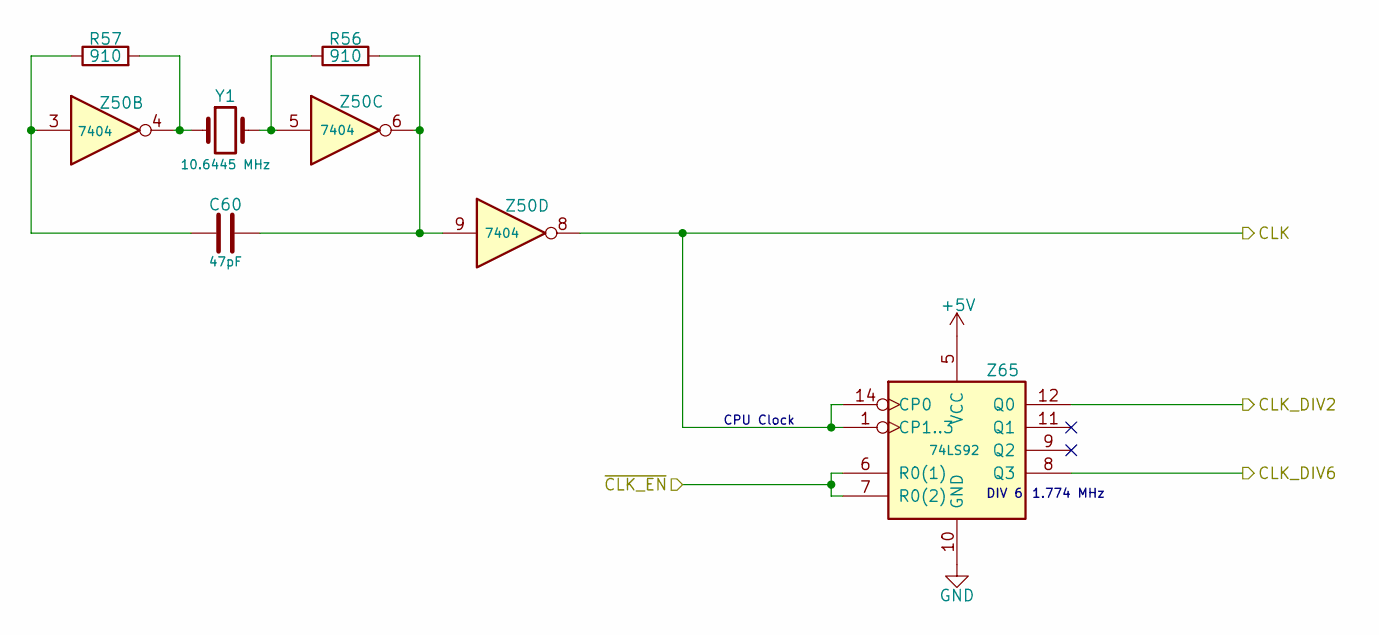
[picture p34: schematic Clock.kicad_sch]

Parts:
C60: 47pF; TRS80_Model_I_C_Disc_9.5L_4W_6P_Jap
R56, R57: 910; TRS80_Model_I_R_0.25W_Jap
Y1: 10.6445 MHz; TRS80_Model_I_Crystal_Jap
Z50: 7404; TRS80_Model_I_DIP14_Jap
Z65: 74LS92; TRS80_Model_I_DIP14_Jap

Connections:
+5V: Z65.5 (VCC)
CLK: Z50.8, Z65.1 (CP1..3), Z65.14 (CP0)
CLK_DIV2: Z65.12 (Q0)
CLK_DIV6: Z65.8 (Q3)
GND: Z65.10 (GND)
unnamed: C60.1, R57.1, Z50.3
unnamed: C60.2, R56.2, Z50.6, Z50.9
unnamed: R56.1, Y1.2, Z50.5
unnamed: R57.2, Y1.1, Z50.4
~CLK_EN: Z65.6 (R0(1)), Z65.7 (R0(2))

Notes on the sheet:
CPU Clock
DIV 6
1.774 MHz
