RetroStack/TRS-80-Model-I-Jap20-E1/KiCAD/Power.kicad_sch

## KiCad design KiCAD/Power.kicad_sch (2025-06-16)

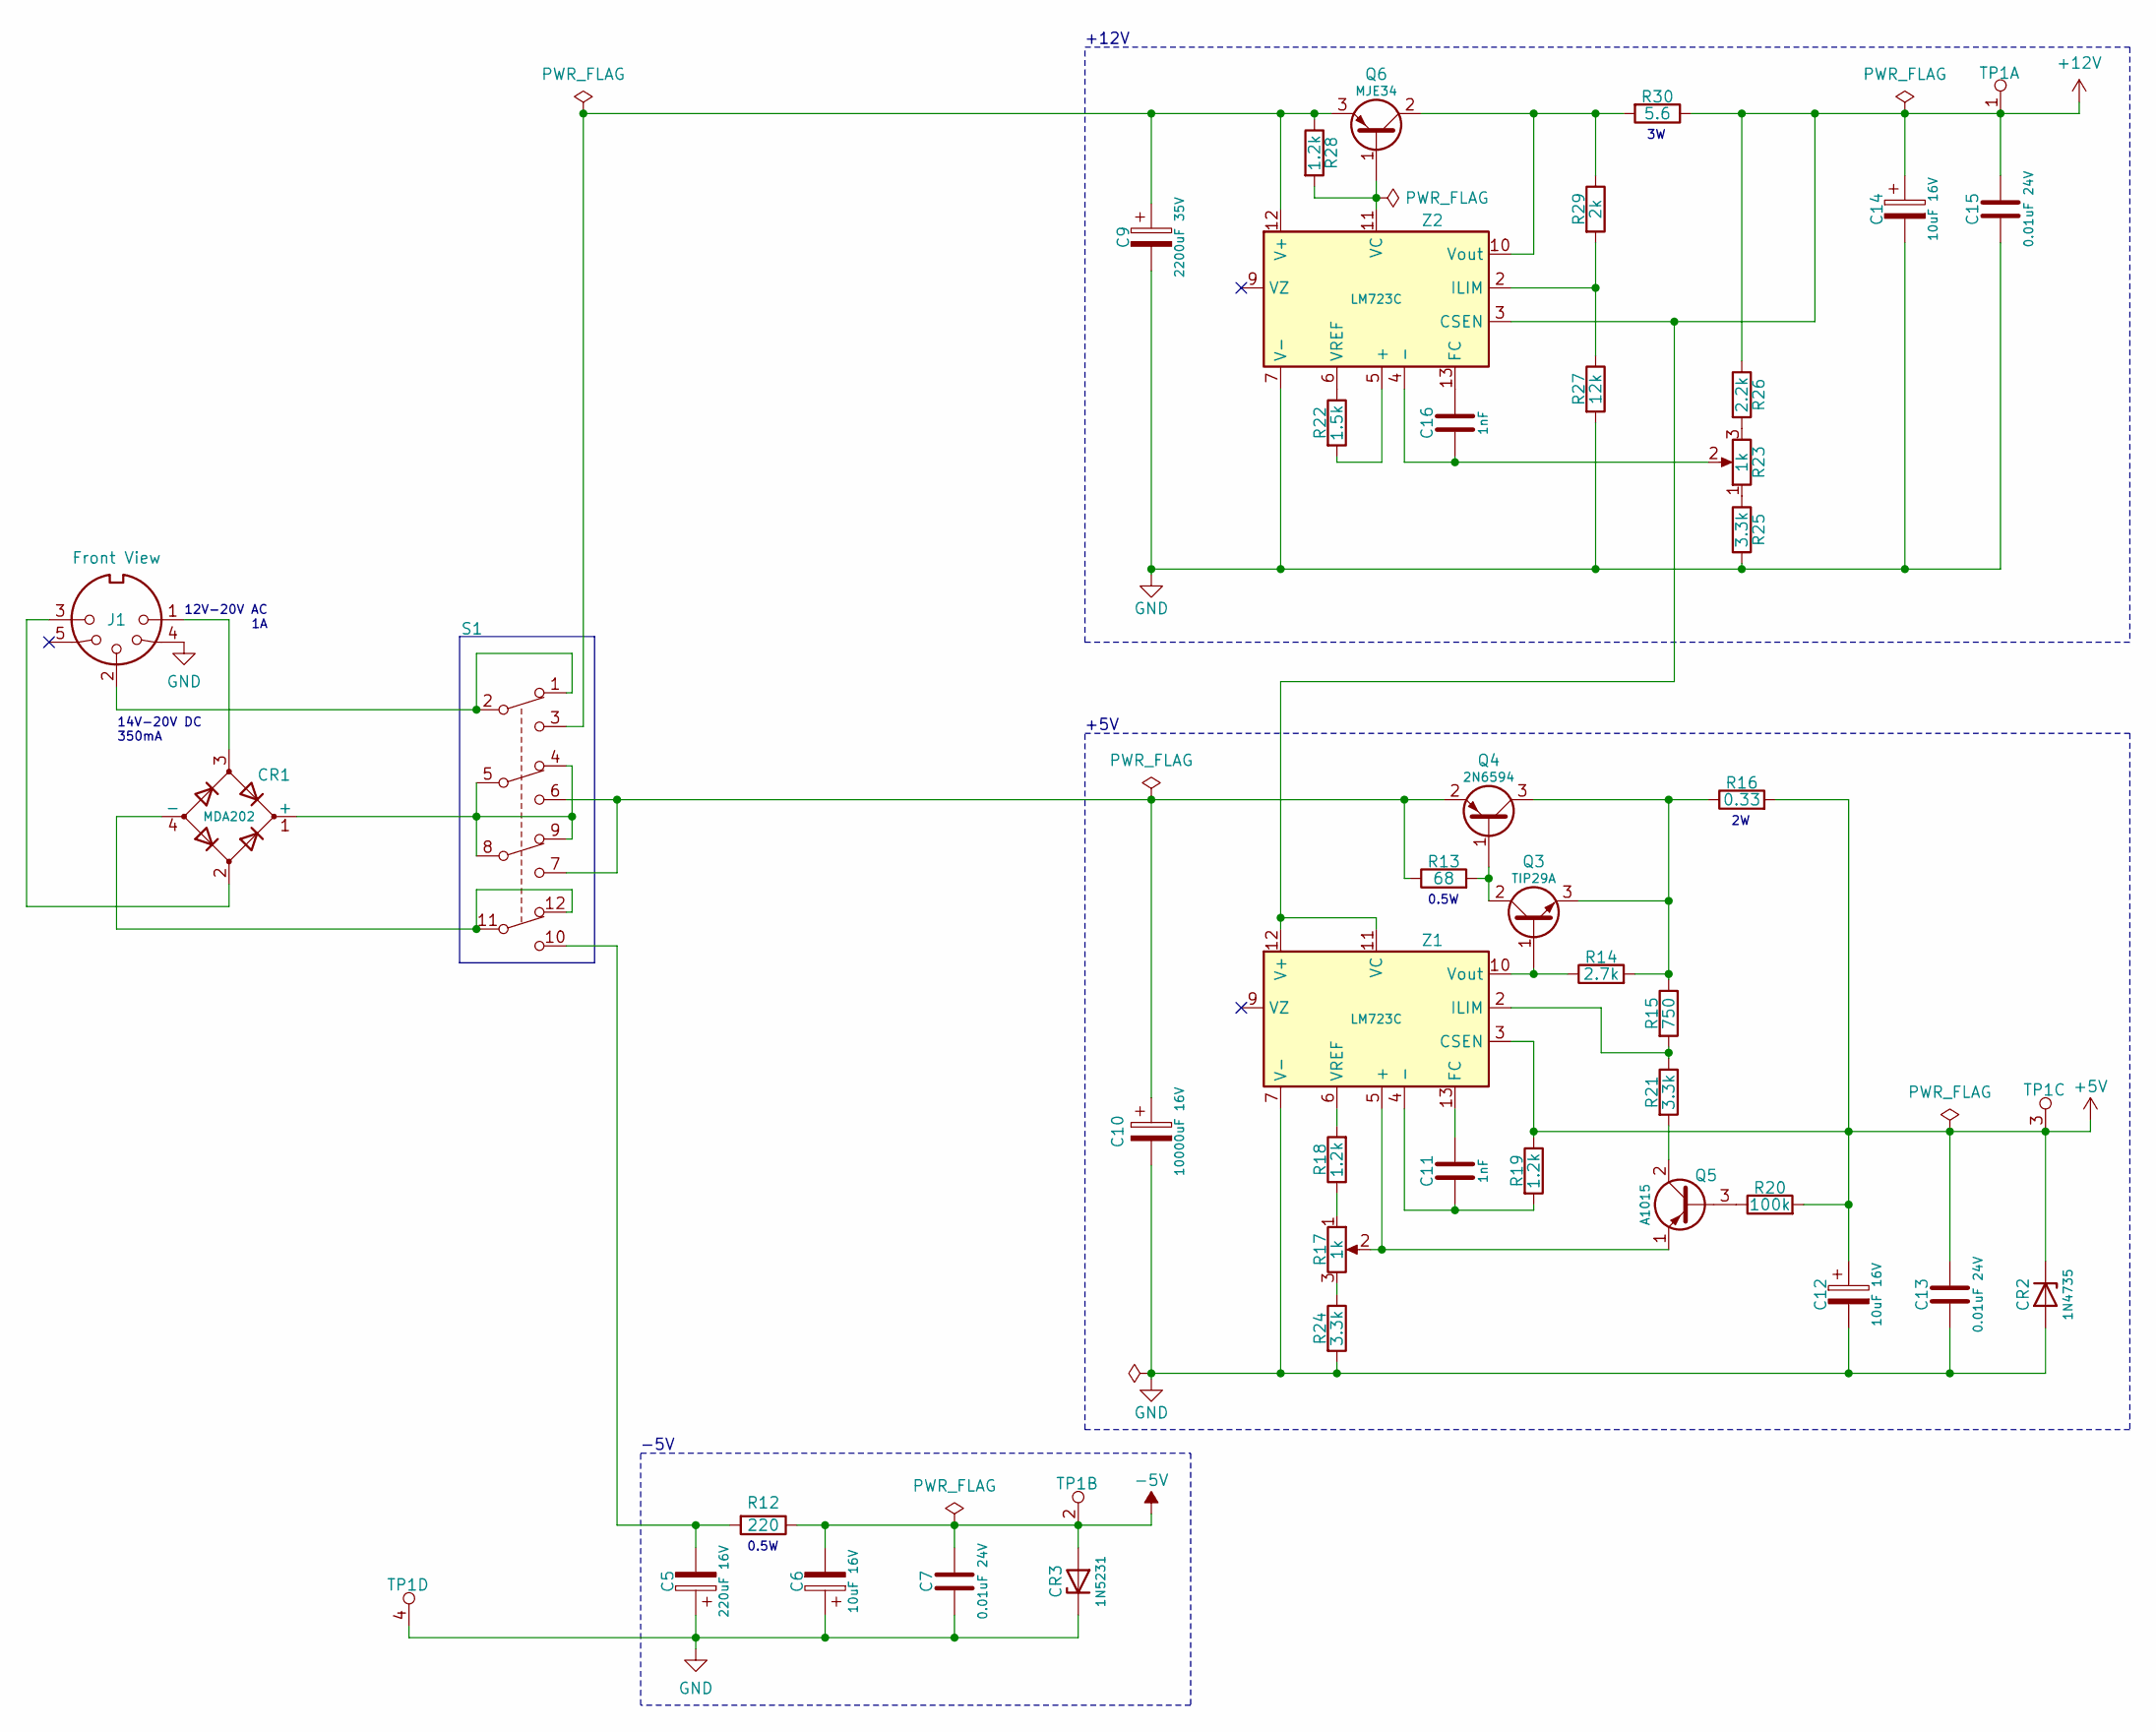
[picture p35: schematic Power.kicad_sch]

Parts:
C5: 220uF 16V; TRS80_Model_I_C_Pol_Radial_10D_5P_Jap
C6, C12, C14: 10uF 16V; TRS80_Model_I_C_Pol_Radial_5D_2.5P_Jap
C7, C13, C15: 0.01uF 24V; TRS80_Model_I_C_Disc_9.5L_4W_6P_Jap
C9: 2200uF 35V; TRS80_Model_I_C_Pol_Axial_41L_19W_48P_Jap
C10: 10000uF 16V; TRS80_Model_I_C_Pol_Axial_63L_25W_71P_Jap
C11, C16: 1nF; TRS80_Model_I_C_Disc_9.5L_4W_6P_Small_Jap
CR1: MDA202; TRS80_Model_I_D_Bridge_Jap
CR2: 1N4735; TRS80_Model_I_D_Zener_Long_Jap
CR3: 1N5231; TRS80_Model_I_D_Zener_Jap
J1: Front View; TRS80_Model_I_DIN5_Jap
Q3: TIP29A; TRS80_Model_I_Q_Box_BCE_Jap
Q4: 2N6594; TRS80_Model_I_Q_Heatsink_Large_BEC_Jap
Q5: A1015; TRS80_Model_I_Q_Circle_ECB_Jap
Q6: MJE34; TRS80_Model_I_Q_Heatsink_Small_BCE_Jap
R12: 220; TRS80_Model_I_R_0.5W_Jap
R13: 68; TRS80_Model_I_R_0.5W_Jap
R14: 2.7k; TRS80_Model_I_R_0.25W_Jap
R15: 750; TRS80_Model_I_R_0.25W_Jap
R16: 0.33; TRS80_Model_I_R_2W_Jap
R17, R23: 1k; TRS80_Model_I_R_Pot_Jap
R18, R19, R28: 1.2k; TRS80_Model_I_R_0.25W_Jap
R20: 100k; TRS80_Model_I_R_0.25W_Jap
R21, R24, R25: 3.3k; TRS80_Model_I_R_0.25W_Jap
R22: 1.5k; TRS80_Model_I_R_0.25W_Jap
R26: 2.2k; TRS80_Model_I_R_0.25W_Jap
R27: 12k; TRS80_Model_I_R_0.25W_Jap
R29: 2k; TRS80_Model_I_R_0.25W_Jap
R30: 5.6; TRS80_Model_I_R_3W_Jap
S1: TRS80_Model_I_Sw_Large_Jap
TP1: TRS80_Model_I_TestPoints
Z1, Z2: LM723C; TRS80_Model_I_DIP14_Jap

Connections:
+5V: C12.1, C13.1, CR2.1 (K), R16.2, R19.1, R20.2, TP1.3, Z1.3 (CSEN)
+12V: C14.1, C15.1, R26.1, R30.1, TP1.1, Z1.11 (VC), Z1.12 (V+), Z2.3 (CSEN)
-5V: C6.2, C7.1, CR3.2 (A), R12.1, TP1.2
GND: C5.1, C6.1, C7.2, C9.2, C10.2, C12.2, C13.2, C14.2, C15.2, CR2.2 (A), CR3.1 (K), J1.4, R24.2, R25.2, R27.2, TP1.4, Z1.7 (V-), Z2.7 (V-)
unnamed: C5.2, R12.2, S1.10
unnamed: C9.1, Q6.3 (E), R28.1, S1.3, Z2.12 (V+)
unnamed: C10.1, Q4.2 (E), R13.1, S1.6, S1.7
unnamed: C11.1, R19.2, Z1.4 (-)
unnamed: C11.2, Z1.13 (FC)
unnamed: C16.1, Z2.13 (FC)
unnamed: C16.2, R23.2, Z2.4 (-)
unnamed: CR1.1 (+), S1.4, S1.5, S1.8, S1.9
unnamed: CR1.2, J1.3
unnamed: CR1.3, J1.1
unnamed: CR1.4 (-), S1.11, S1.12
unnamed: J1.2, S1.1, S1.2
unnamed: Q3.1 (B), R14.1, Z1.10 (Vout)
unnamed: Q3.2 (C), Q4.1 (B), R13.2
unnamed: Q3.3 (E), Q4.3 (C), R14.2, R15.1, R16.1
unnamed: Q5.1 (E), R17.2, Z1.5 (+)
unnamed: Q5.2 (C), R21.2
unnamed: Q5.3 (B), R20.1
unnamed: Q6.1 (B), R28.2, Z2.11 (VC)
unnamed: Q6.2 (C), R29.1, R30.2, Z2.10 (Vout)
unnamed: R15.2, R21.1, Z1.2 (ILIM)
unnamed: R17.1, R18.1
unnamed: R17.3, R24.1
unnamed: R18.2, Z1.6 (VREF)
unnamed: R22.1, Z2.6 (VREF)
unnamed: R22.2, Z2.5 (+)
unnamed: R23.1, R25.1
unnamed: R23.3, R26.2
unnamed: R27.1, R29.2, Z2.2 (ILIM)

Notes on the sheet:
+5V
12V-20V AC 1A
0.5W
-5V
+12V
14V-20V DC 350mA
