RetroStack/TRS-80-Model-I-Jap20-E1/KiCAD/RAM.kicad_sch

## KiCad design KiCAD/RAM.kicad_sch (2025-06-16)

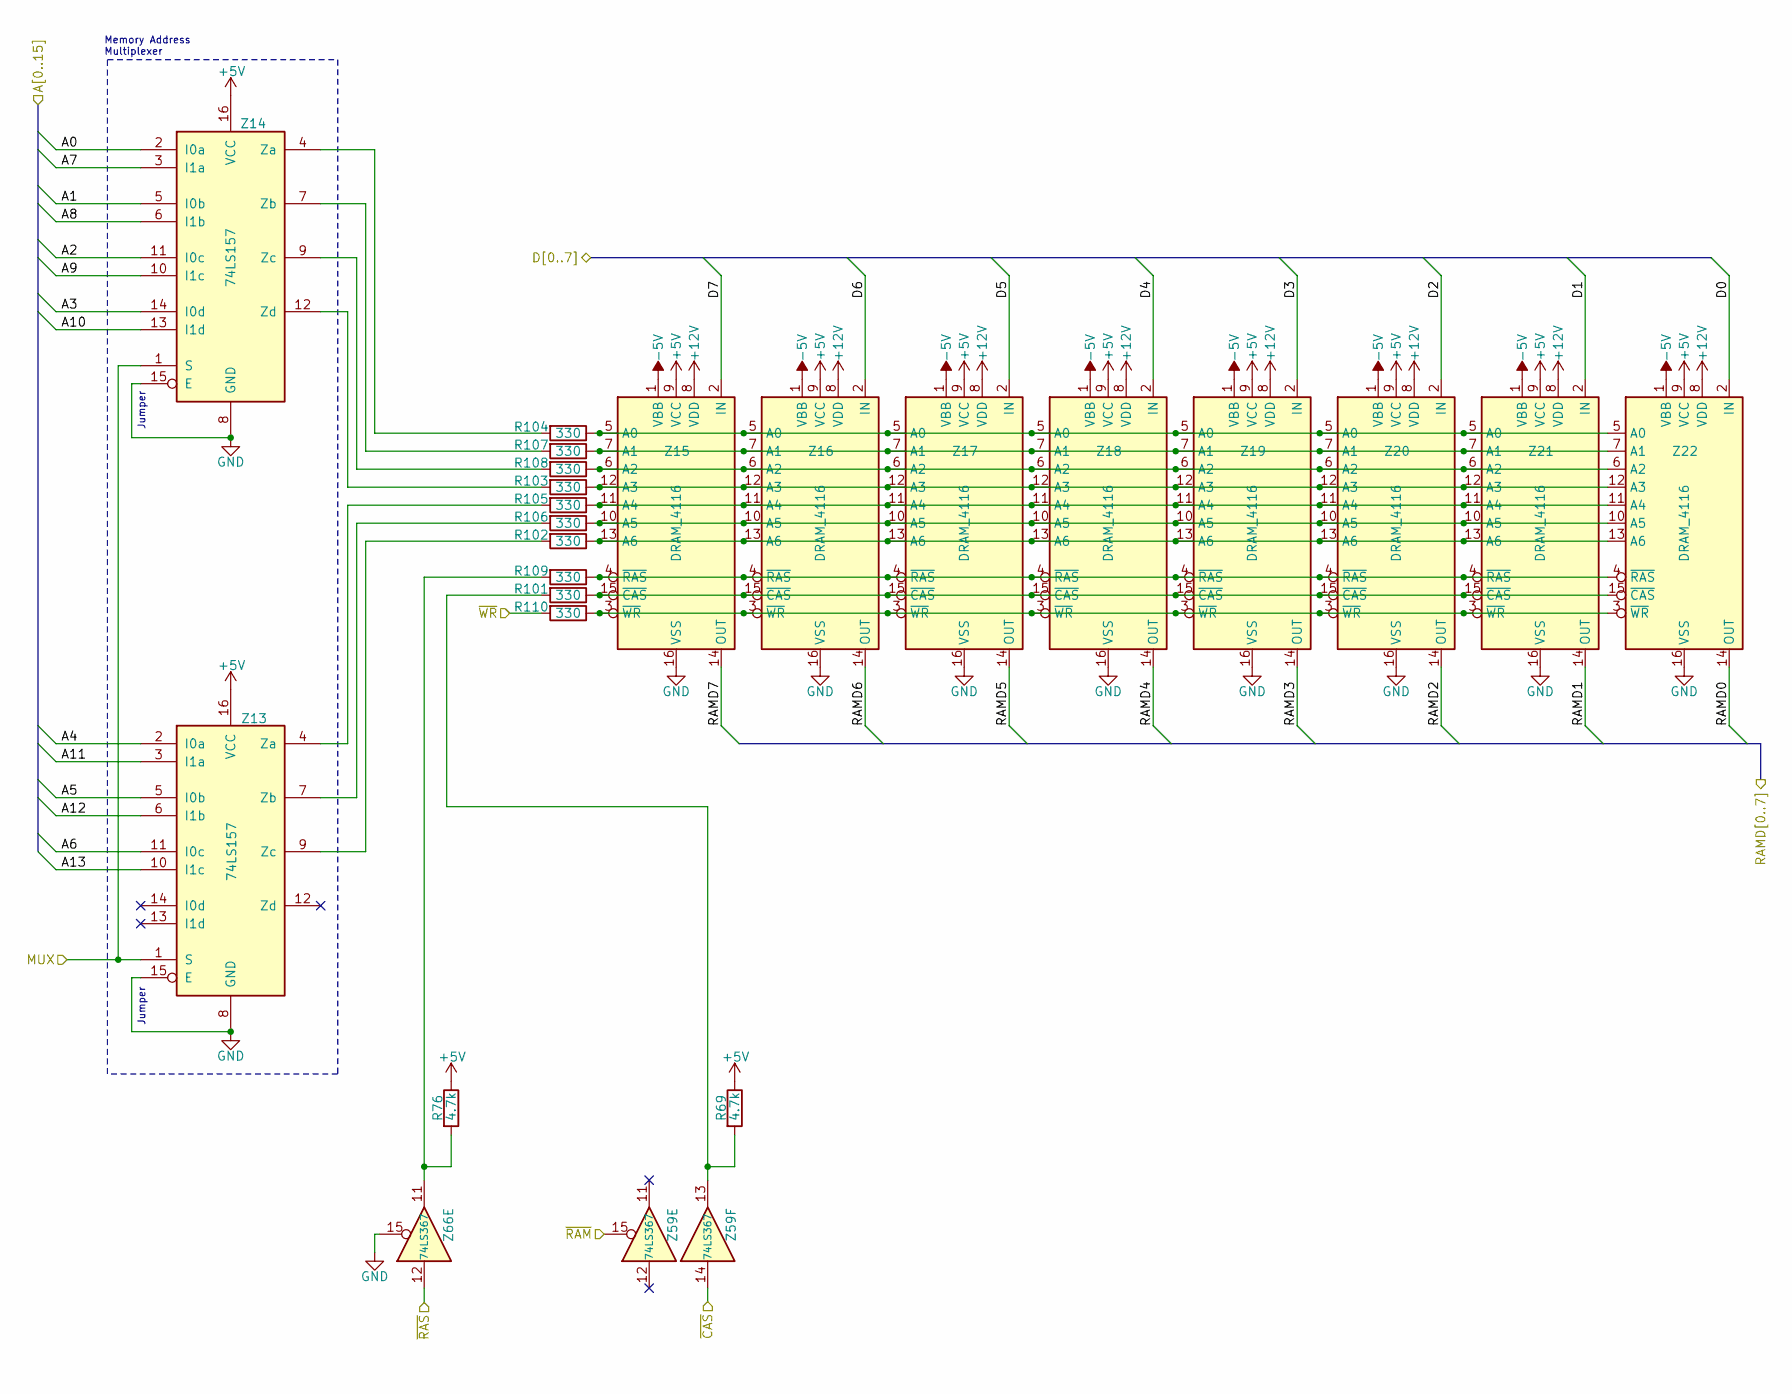
[picture p36: schematic RAM.kicad_sch]

Parts:
R69, R76: 4.7k; TRS80_Model_I_R_0.25W_Jap
R101, R102, R103, R104, R105, R106, R107, R108, R109, R110: 330; TRS80_Model_I_R_0.25W_Jap
Z13, Z14: 74LS157; TRS80_Model_I_DIP16_Jap
Z15, Z16, Z17, Z18, Z19, Z20, Z21, Z22: DRAM_4116; TRS80_Model_I_DIP16_Jap
Z59, Z66: 74LS367; TRS80_Model_I_DIP16_Jap

Connections:
+5V: R69.1, R76.1, Z13.16 (VCC), Z14.16 (VCC), Z15.9 (VCC), Z16.9 (VCC), Z17.9 (VCC), Z18.9 (VCC), Z19.9 (VCC), Z20.9 (VCC), Z21.9 (VCC), Z22.9 (VCC)
+12V: Z15.8 (VDD), Z16.8 (VDD), Z17.8 (VDD), Z18.8 (VDD), Z19.8 (VDD), Z20.8 (VDD), Z21.8 (VDD), Z22.8 (VDD)
-5V: Z15.1 (VBB), Z16.1 (VBB), Z17.1 (VBB), Z18.1 (VBB), Z19.1 (VBB), Z20.1 (VBB), Z21.1 (VBB), Z22.1 (VBB)
A0: Z14.2 (I0a)
A1: Z14.5 (I0b)
A2: Z14.11 (I0c)
A3: Z14.14 (I0d)
A4: Z13.2 (I0a)
A5: Z13.5 (I0b)
A6: Z13.11 (I0c)
A7: Z14.3 (I1a)
A8: Z14.6 (I1b)
A9: Z14.10 (I1c)
A10: Z14.13 (I1d)
A11: Z13.3 (I1a)
A12: Z13.6 (I1b)
A13: Z13.10 (I1c)
D0: Z22.2 (IN)
D1: Z21.2 (IN)
D2: Z20.2 (IN)
D3: Z19.2 (IN)
D4: Z18.2 (IN)
D5: Z17.2 (IN)
D6: Z16.2 (IN)
D7: Z15.2 (IN)
GND: Z13.8 (GND), Z13.15 (E), Z14.8 (GND), Z14.15 (E), Z15.16 (VSS), Z16.16 (VSS), Z17.16 (VSS), Z18.16 (VSS), Z19.16 (VSS), Z20.16 (VSS), Z21.16 (VSS), Z22.16 (VSS), Z66.15
MUX: Z13.1 (S), Z14.1 (S)
unnamed: R101.1, Z15.15 (~CAS), Z16.15 (~CAS), Z17.15 (~CAS), Z18.15 (~CAS), Z19.15 (~CAS), Z20.15 (~CAS), Z21.15 (~CAS), Z22.15 (~CAS)
unnamed: R69.2, R101.2, Z59.13
unnamed: R102.1, Z15.13 (A6), Z16.13 (A6), Z17.13 (A6), Z18.13 (A6), Z19.13 (A6), Z20.13 (A6), Z21.13 (A6), Z22.13 (A6)
unnamed: R102.2, Z13.9 (Zc)
unnamed: R103.1, Z15.12 (A3), Z16.12 (A3), Z17.12 (A3), Z18.12 (A3), Z19.12 (A3), Z20.12 (A3), Z21.12 (A3), Z22.12 (A3)
unnamed: R103.2, Z14.12 (Zd)
unnamed: R104.1, Z15.5 (A0), Z16.5 (A0), Z17.5 (A0), Z18.5 (A0), Z19.5 (A0), Z20.5 (A0), Z21.5 (A0), Z22.5 (A0)
unnamed: R104.2, Z14.4 (Za)
unnamed: R105.1, Z15.11 (A4), Z16.11 (A4), Z17.11 (A4), Z18.11 (A4), Z19.11 (A4), Z20.11 (A4), Z21.11 (A4), Z22.11 (A4)
unnamed: R105.2, Z13.4 (Za)
unnamed: R106.1, Z15.10 (A5), Z16.10 (A5), Z17.10 (A5), Z18.10 (A5), Z19.10 (A5), Z20.10 (A5), Z21.10 (A5), Z22.10 (A5)
unnamed: R106.2, Z13.7 (Zb)
unnamed: R107.1, Z15.7 (A1), Z16.7 (A1), Z17.7 (A1), Z18.7 (A1), Z19.7 (A1), Z20.7 (A1), Z21.7 (A1), Z22.7 (A1)
unnamed: R107.2, Z14.7 (Zb)
unnamed: R108.1, Z15.6 (A2), Z16.6 (A2), Z17.6 (A2), Z18.6 (A2), Z19.6 (A2), Z20.6 (A2), Z21.6 (A2), Z22.6 (A2)
unnamed: R108.2, Z14.9 (Zc)
unnamed: R109.1, Z15.4 (~RAS), Z16.4 (~RAS), Z17.4 (~RAS), Z18.4 (~RAS), Z19.4 (~RAS), Z20.4 (~RAS), Z21.4 (~RAS), Z22.4 (~RAS)
unnamed: R76.2, R109.2, Z66.11
unnamed: R110.1, Z15.3 (~WR), Z16.3 (~WR), Z17.3 (~WR), Z18.3 (~WR), Z19.3 (~WR), Z20.3 (~WR), Z21.3 (~WR), Z22.3 (~WR)
RAMD0: Z22.14 (OUT)
RAMD1: Z21.14 (OUT)
RAMD2: Z20.14 (OUT)
RAMD3: Z19.14 (OUT)
RAMD4: Z18.14 (OUT)
RAMD5: Z17.14 (OUT)
RAMD6: Z16.14 (OUT)
RAMD7: Z15.14 (OUT)
~CAS: Z59.14
~RAM: Z59.15
~RAS: Z66.12
~WR: R110.2

Notes on the sheet:
Memory Address Multiplexer
Jumper
