RetroStack/TRS-80-Model-I-Jap20-E1/KiCAD/RAM_ROM_Interface.kicad_sch

## KiCad design KiCAD/RAM_ROM_Interface.kicad_sch (2025-06-16)

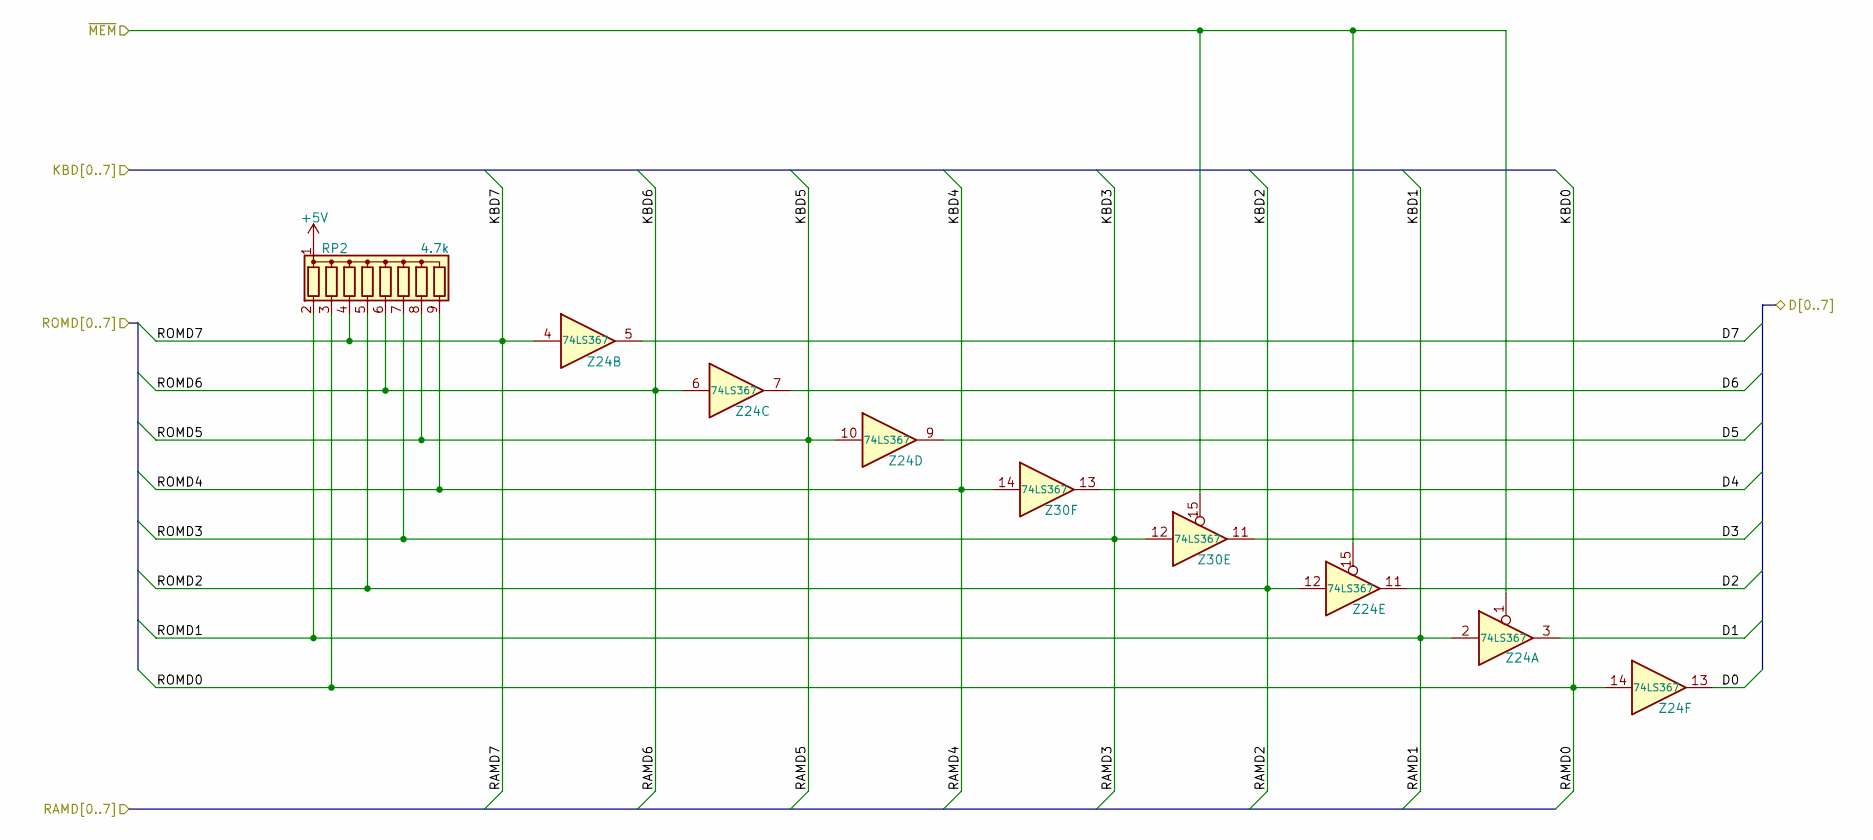
[picture p37: schematic RAM_ROM_Interface.kicad_sch]

Parts:
RP2: 4.7k; TRS80_Model_I_R_Array_09_Jap
Z24, Z30: 74LS367; TRS80_Model_I_DIP16_Jap

Connections:
+5V: RP2.1 (common)
D0: Z24.13
D1: Z24.3
D2: Z24.11
D3: Z30.11
D4: Z30.13
D5: Z24.9
D6: Z24.7
D7: Z24.5
KBD0: RP2.3 (R2), Z24.14
KBD1: RP2.2 (R1), Z24.2
KBD2: RP2.5 (R4), Z24.12
KBD3: RP2.7 (R6), Z30.12
KBD4: RP2.9 (R8), Z30.14
KBD5: RP2.8 (R7), Z24.10
KBD6: RP2.6 (R5), Z24.6
KBD7: RP2.4 (R3), Z24.4
~MEM: Z24.1, Z24.15, Z30.15
