RetroStack/TRS-80-Model-I-Jap20-E1/KiCAD/ROM.kicad_sch

## KiCad design KiCAD/ROM.kicad_sch (2025-06-16)

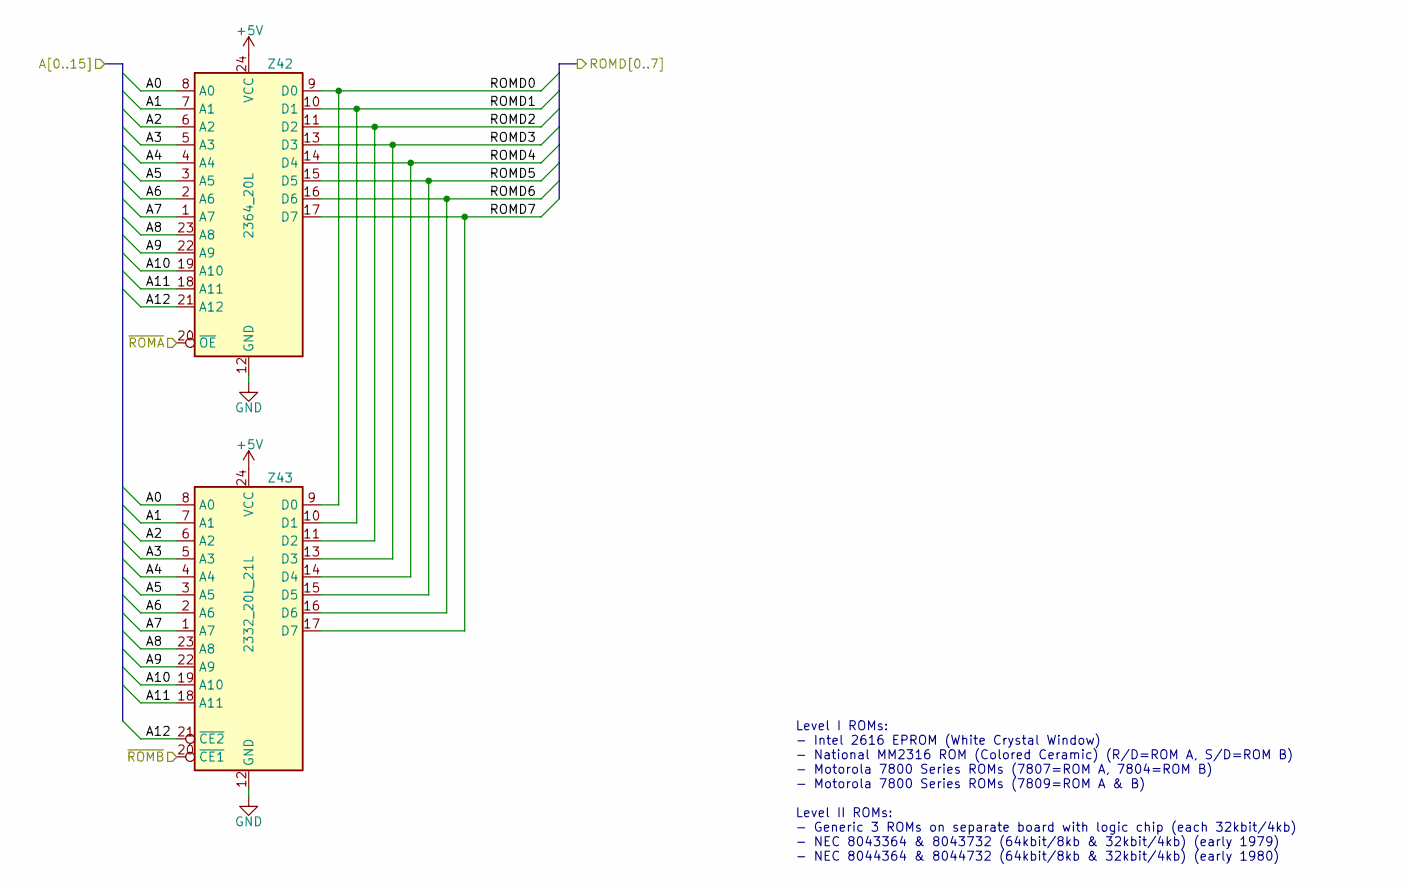
[picture p38: schematic ROM.kicad_sch]

Parts:
Z42: 2364_20L; TRS80_Model_I_DIP24_Jap
Z43: 2332_20L_21L; TRS80_Model_I_DIP24_Jap

Connections:
+5V: Z42.24 (VCC), Z43.24 (VCC)
A0: Z42.8 (A0), Z43.8 (A0)
A1: Z42.7 (A1), Z43.7 (A1)
A2: Z42.6 (A2), Z43.6 (A2)
A3: Z42.5 (A3), Z43.5 (A3)
A4: Z42.4 (A4), Z43.4 (A4)
A5: Z42.3 (A5), Z43.3 (A5)
A6: Z42.2 (A6), Z43.2 (A6)
A7: Z42.1 (A7), Z43.1 (A7)
A8: Z42.23 (A8), Z43.23 (A8)
A9: Z42.22 (A9), Z43.22 (A9)
A10: Z42.19 (A10), Z43.19 (A10)
A11: Z42.18 (A11), Z43.18 (A11)
A12: Z42.21 (A12), Z43.21 (~CE2)
GND: Z42.12 (GND), Z43.12 (GND)
ROMD0: Z42.9 (D0), Z43.9 (D0)
ROMD1: Z42.10 (D1), Z43.10 (D1)
ROMD2: Z42.11 (D2), Z43.11 (D2)
ROMD3: Z42.13 (D3), Z43.13 (D3)
ROMD4: Z42.14 (D4), Z43.14 (D4)
ROMD5: Z42.15 (D5), Z43.15 (D5)
ROMD6: Z42.16 (D6), Z43.16 (D6)
ROMD7: Z42.17 (D7), Z43.17 (D7)
~ROMA: Z42.20 (~OE)
~ROMB: Z43.20 (~CE1)

Notes on the sheet:
Level I ROMs: - Intel 2616 EPROM (White Crystal Window) - National MM2316 ROM (Colored Ceramic) (R/D=ROM A, S/D=ROM B) - Motorola 7800 Series ROMs (7807=ROM A, 7804=ROM B) - Motorola 7800 Series ROMs (7809=ROM A & B) Level II ROMs: - Generic 3 ROMs on separate board with logic chip (each 32kbit/4kb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
