RetroStack/TRS-80-Model-I-Jap20-E1/KiCAD/TRS80_Model_I_Jap20_E1.kicad_sch

## KiCad design KiCAD/TRS80_Model_I_Jap20_E1.kicad_sch (2025-06-16)

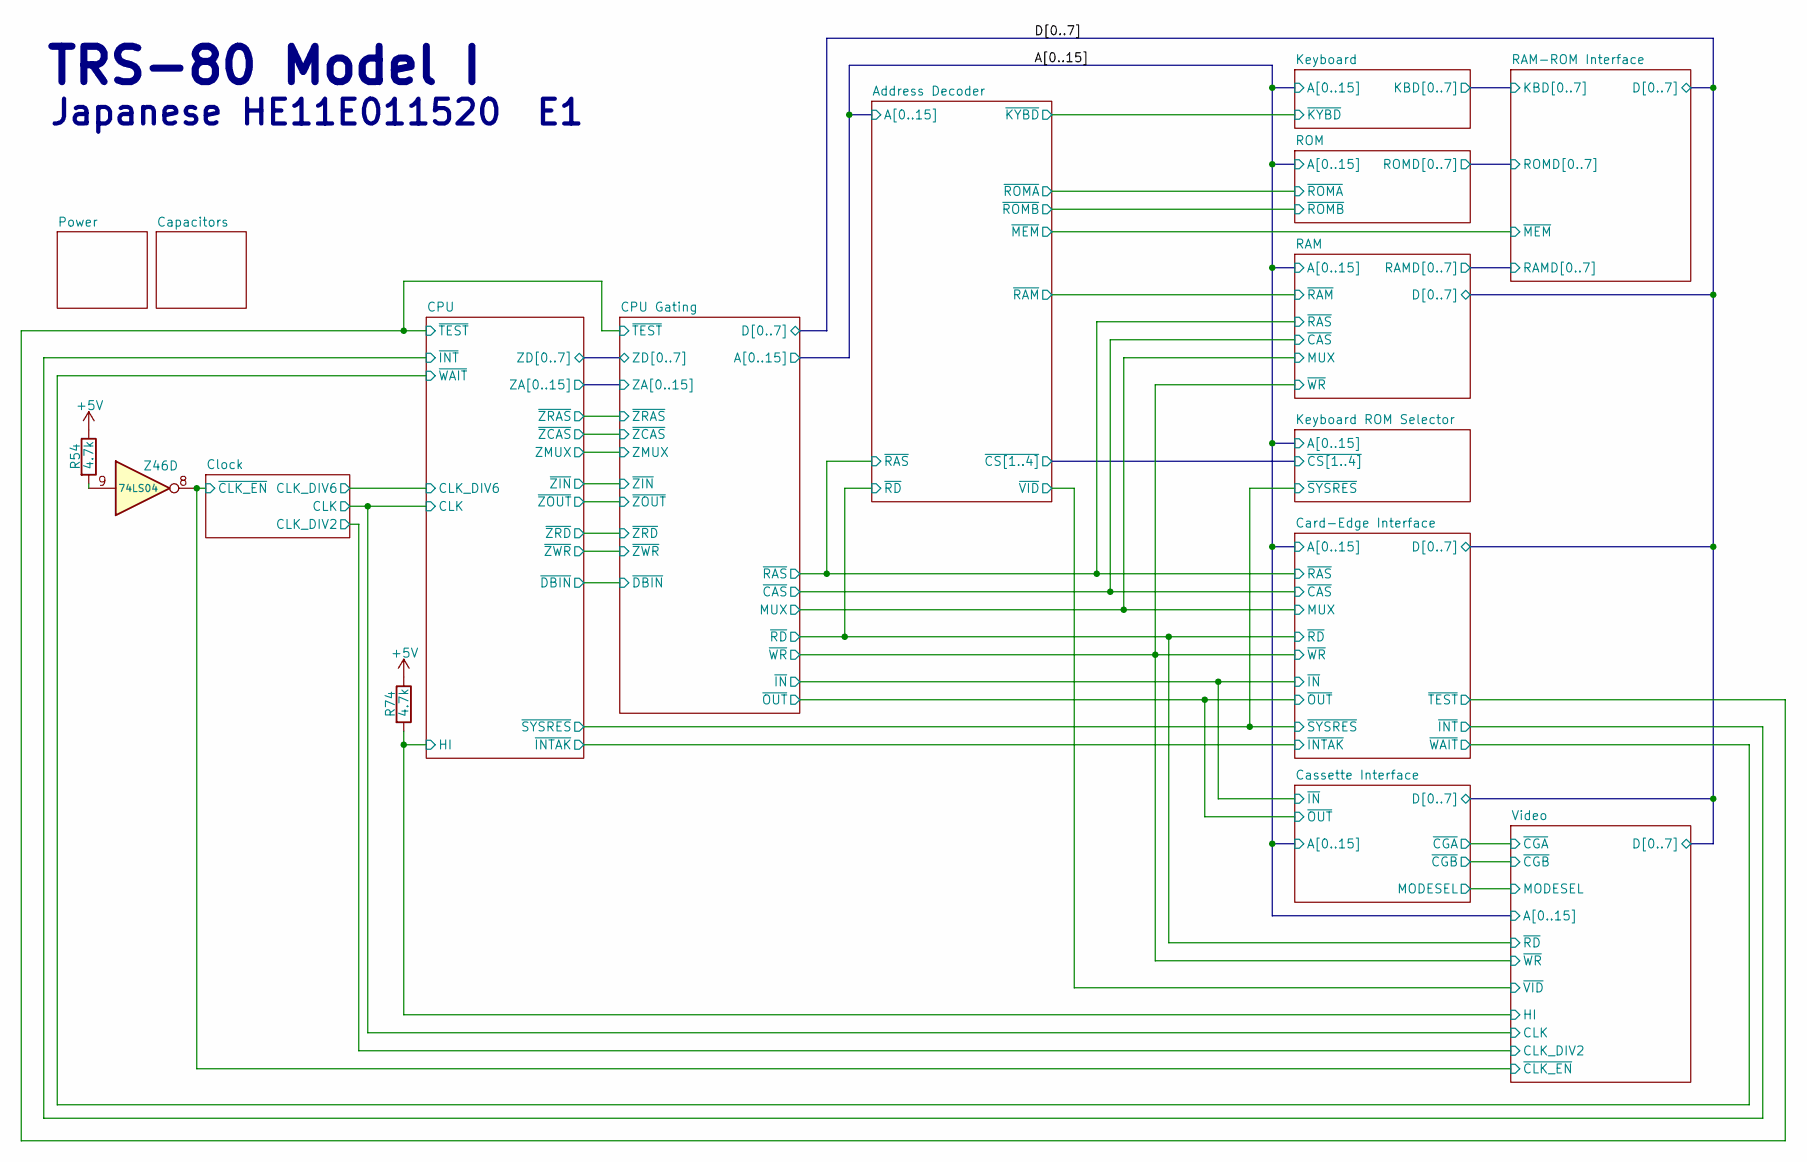
[picture p39: schematic TRS80_Model_I_Jap20_E1.kicad_sch]

Parts:
R54, R74: 4.7k; TRS80_Model_I_R_0.25W_Jap
Z46: 74LS04; TRS80_Model_I_DIP14_Jap

Connections:
+5V: R54.1, R74.1
HI: R74.2
unnamed: R54.2, Z46.9
~CLK_EN: Z46.8

Notes on the sheet:
TRS-80 Model I
Japanese HE11E011520
