RetroStack/TRS-80-Model-I-Jap20-E1/KiCAD/Video Latch.kicad_sch

## KiCad design KiCAD/Video Latch.kicad_sch (2025-06-16)

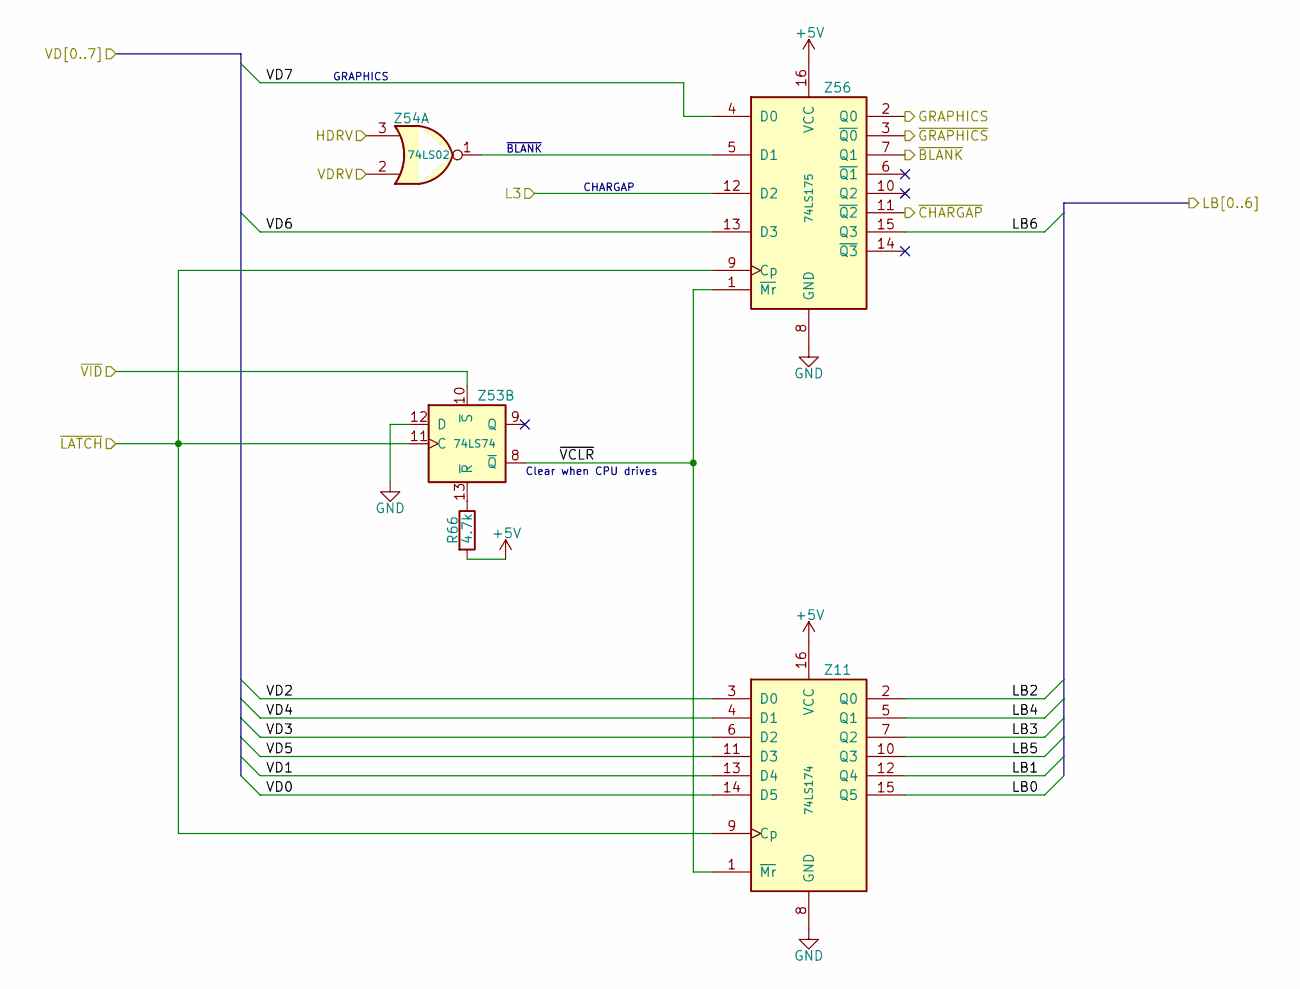
[picture p40: schematic Video Latch.kicad_sch]

Parts:
R66: 4.7k; TRS80_Model_I_R_0.25W_Jap
Z11: 74LS174; TRS80_Model_I_DIP16_Jap
Z53: 74LS74; TRS80_Model_I_DIP14_Jap
Z54: 74LS02; TRS80_Model_I_DIP14_Jap
Z56: 74LS175; TRS80_Model_I_DIP16_Jap

Connections:
+5V: R66.2, Z11.16 (VCC), Z56.16 (VCC)
GND: Z11.8 (GND), Z53.12 (D), Z56.8 (GND)
GRAPHICS: Z56.2 (Q0)
HDRV: Z54.3
L3: Z56.12 (D2)
LB0: Z11.15 (Q5)
LB1: Z11.12 (Q4)
LB2: Z11.2 (Q0)
LB3: Z11.7 (Q2)
LB4: Z11.5 (Q1)
LB5: Z11.10 (Q3)
LB6: Z56.15 (Q3)
unnamed: R66.1, Z53.13 (~R)
unnamed: Z54.1, Z56.5 (D1)
VD0: Z11.14 (D5)
VD1: Z11.13 (D4)
VD2: Z11.3 (D0)
VD3: Z11.6 (D2)
VD4: Z11.4 (D1)
VD5: Z11.11 (D3)
VD6: Z56.13 (D3)
VD7: Z56.4 (D0)
VDRV: Z54.2
~BLANK: Z56.7 (Q1)
~CHARGAP: Z56.11 (~Q2)
~GRAPHICS: Z56.3 (~Q0)
~LATCH: Z11.9 (Cp), Z53.11 (C), Z56.9 (Cp)
~VCLR: Z11.1 (~Mr), Z53.8 (~Q), Z56.1 (~Mr)
~VID: Z53.10 (~S)

Notes on the sheet:
CHARGAP
GRAPHICS
Clear when CPU drives
~{BLANK}
