RetroStack/TRS-80-Model-I-Jap20-E1/KiCAD/VideoAccessMultiplexer.kicad_sch

## KiCad design KiCAD/VideoAccessMultiplexer.kicad_sch (2025-06-16)

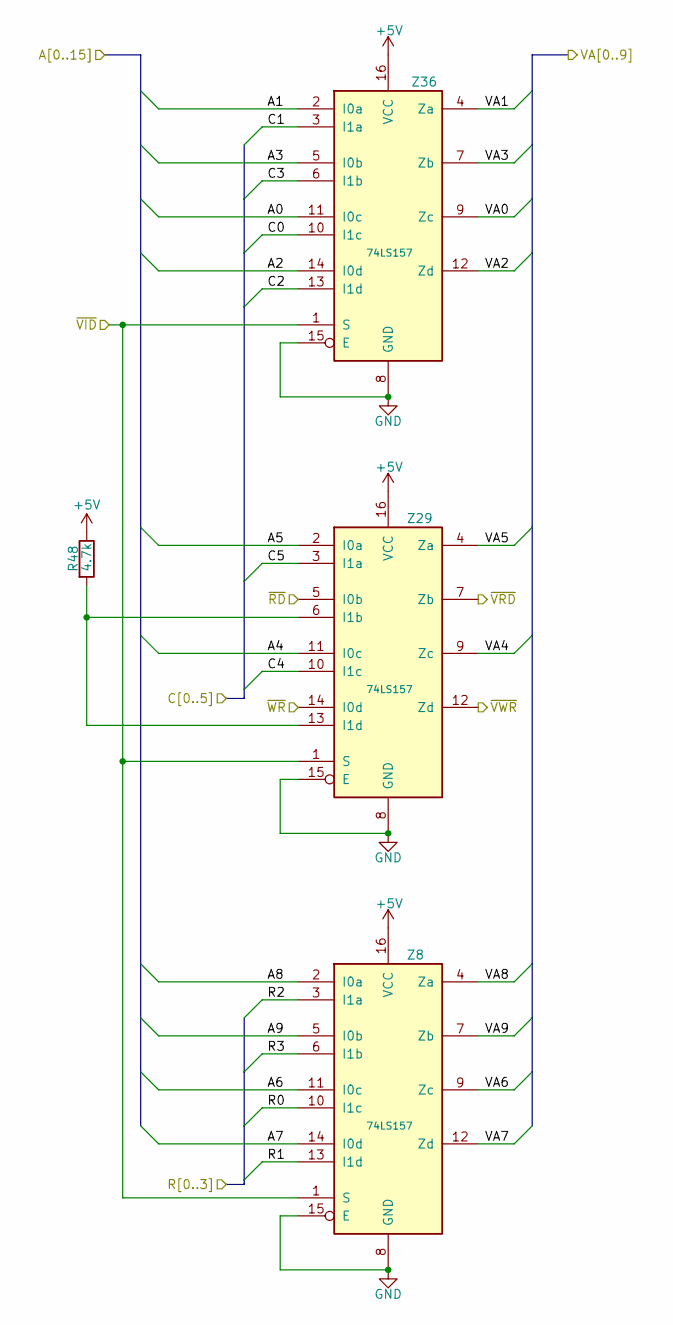
[picture p41: schematic VideoAccessMultiplexer.kicad_sch]

Parts:
R48: 4.7k; TRS80_Model_I_R_0.25W_Jap
Z8, Z29, Z36: 74LS157; TRS80_Model_I_DIP16_Jap

Connections:
+5V: R48.1, Z8.16 (VCC), Z29.16 (VCC), Z36.16 (VCC)
A0: Z36.11 (I0c)
A1: Z36.2 (I0a)
A2: Z36.14 (I0d)
A3: Z36.5 (I0b)
A4: Z29.11 (I0c)
A5: Z29.2 (I0a)
A6: Z8.11 (I0c)
A7: Z8.14 (I0d)
A8: Z8.2 (I0a)
A9: Z8.5 (I0b)
C0: Z36.10 (I1c)
C1: Z36.3 (I1a)
C2: Z36.13 (I1d)
C3: Z36.6 (I1b)
C4: Z29.10 (I1c)
C5: Z29.3 (I1a)
GND: Z8.8 (GND), Z8.15 (E), Z29.8 (GND), Z29.15 (E), Z36.8 (GND), Z36.15 (E)
unnamed: R48.2, Z29.6 (I1b), Z29.13 (I1d)
R0: Z8.10 (I1c)
R1: Z8.13 (I1d)
R2: Z8.3 (I1a)
R3: Z8.6 (I1b)
VA0: Z36.9 (Zc)
VA1: Z36.4 (Za)
VA2: Z36.12 (Zd)
VA3: Z36.7 (Zb)
VA4: Z29.9 (Zc)
VA5: Z29.4 (Za)
VA6: Z8.9 (Zc)
VA7: Z8.12 (Zd)
VA8: Z8.4 (Za)
VA9: Z8.7 (Zb)
~RD: Z29.5 (I0b)
~VID: Z8.1 (S), Z29.1 (S), Z36.1 (S)
~VRD: Z29.7 (Zb)
~VWR: Z29.12 (Zd)
~WR: Z29.14 (I0d)
