RetroStack/TRS-80-Model-I-Jap20-E1/KiCAD/VideoCounter.kicad_sch

## KiCad design KiCAD/VideoCounter.kicad_sch (2025-06-16)

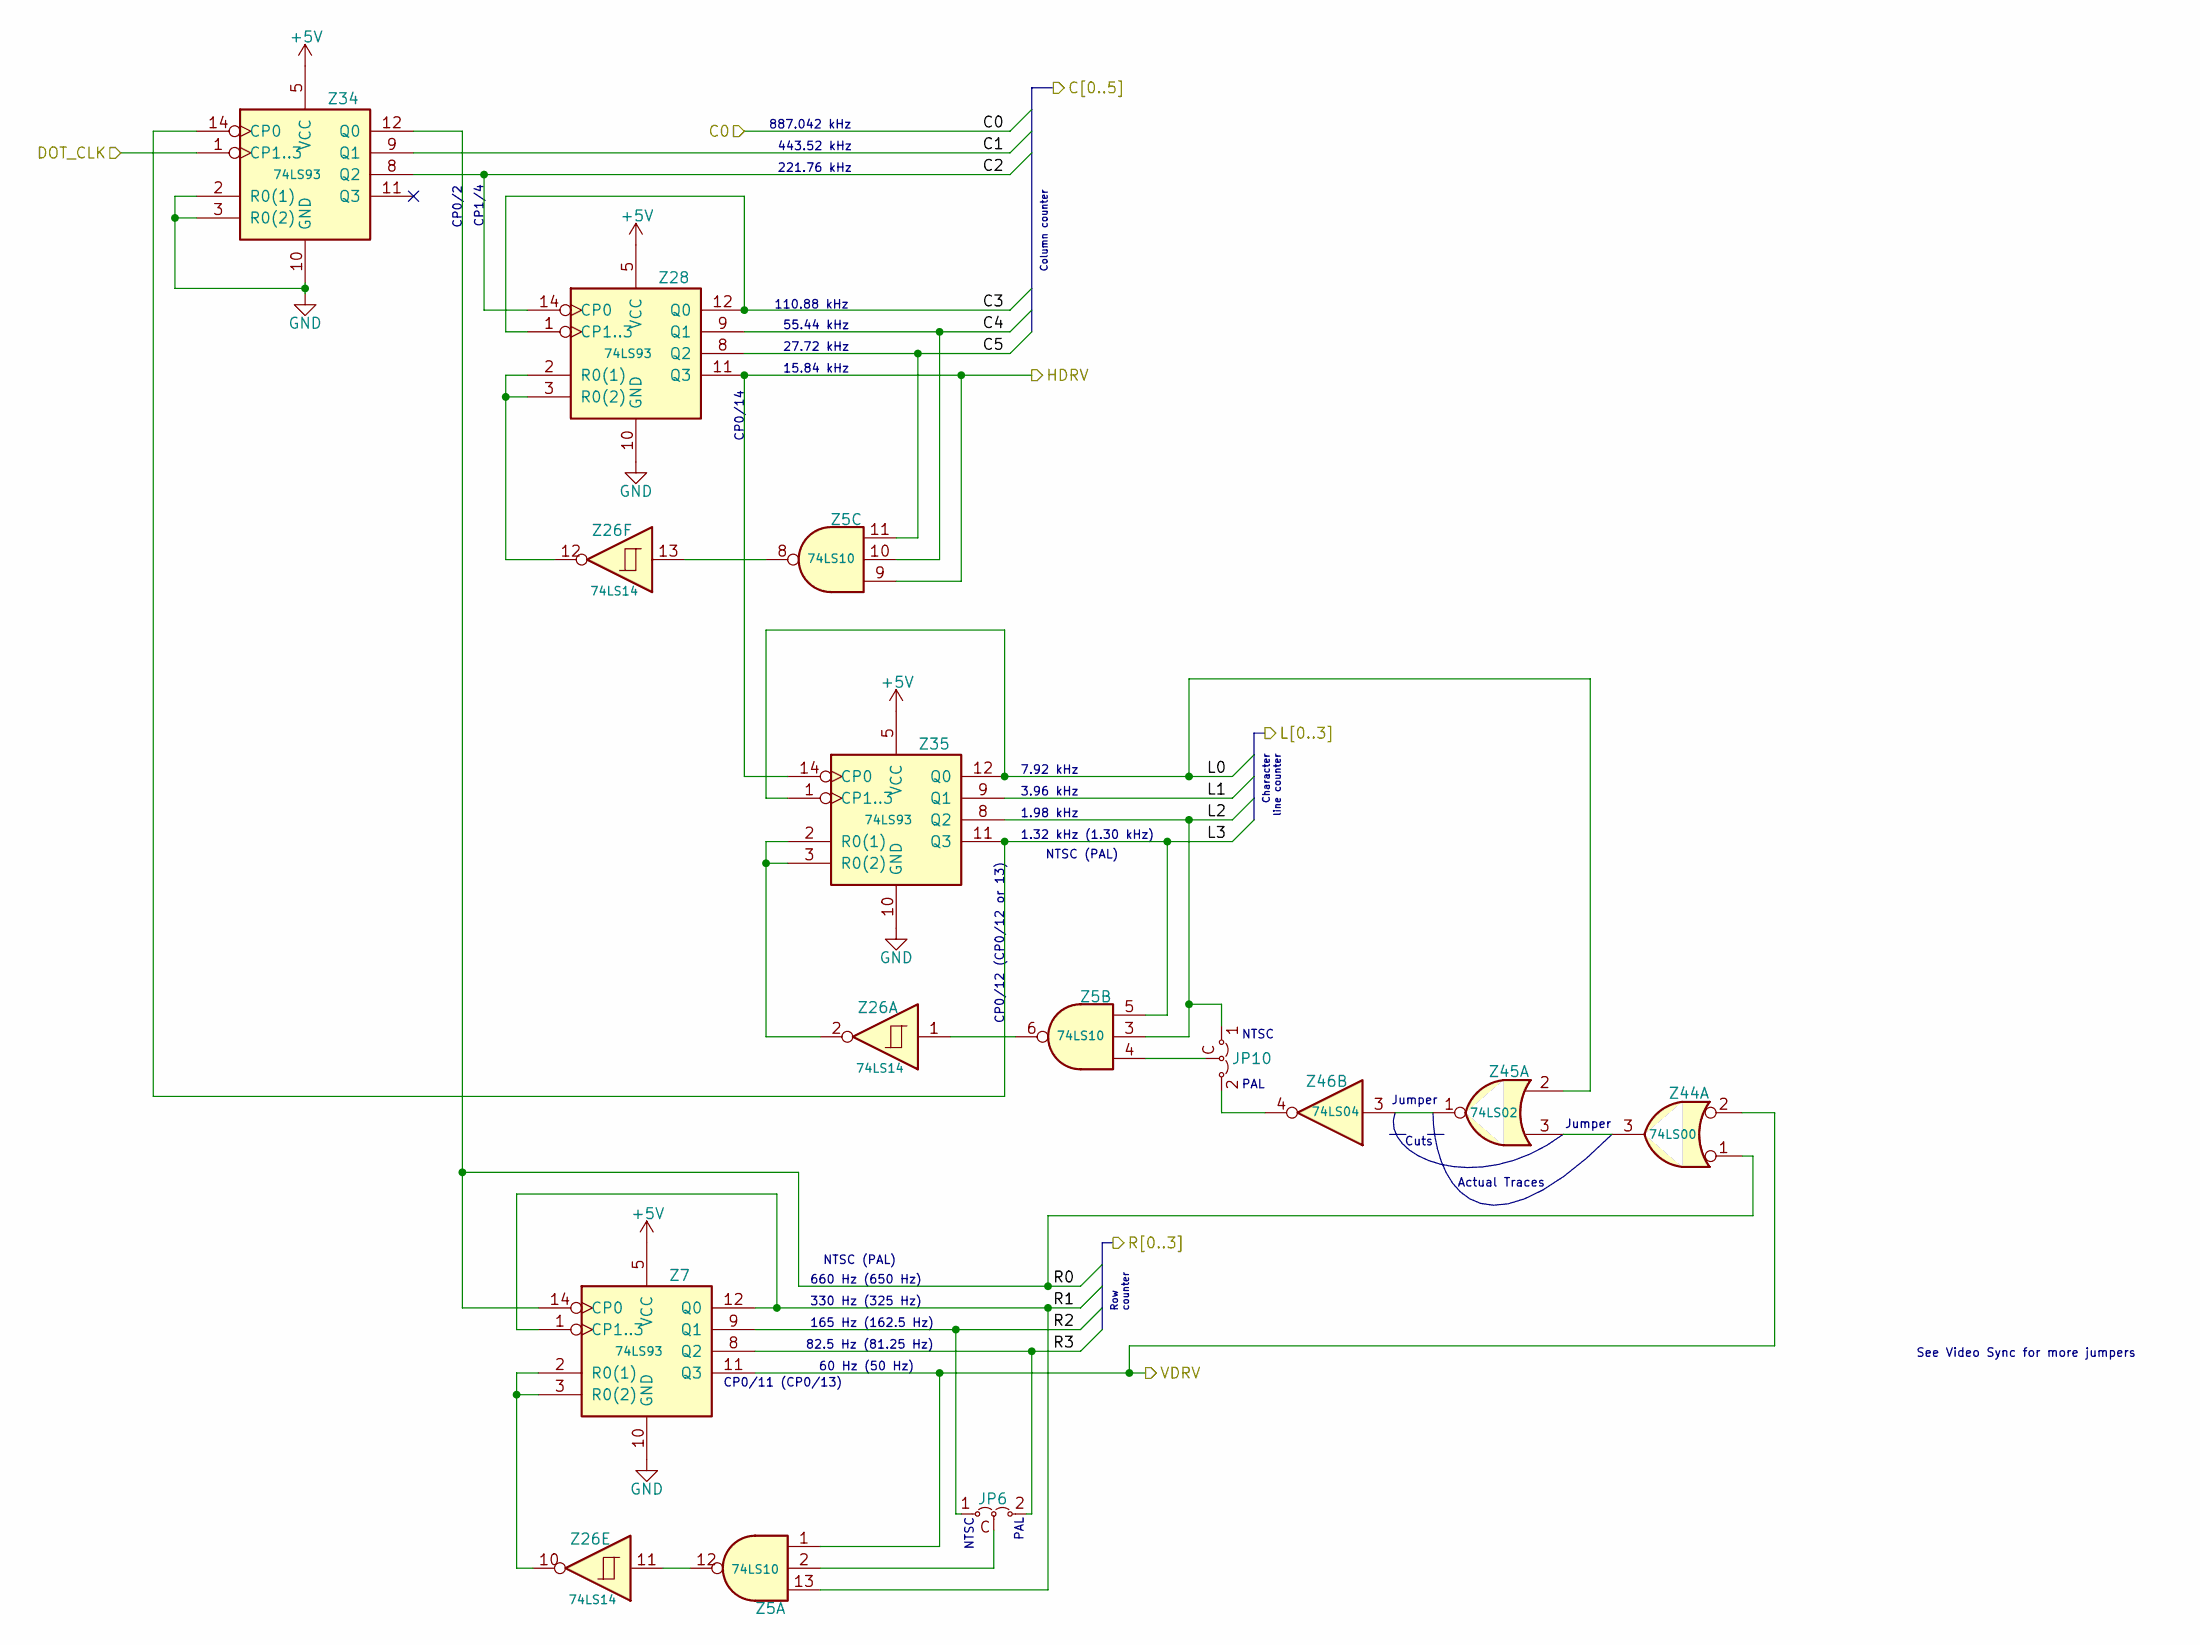
[picture p42: schematic VideoCounter.kicad_sch]

Parts:
JP6: TRS80_Model_I_Jumper_3_Jap; TRS80_Model_I_Jumper_3_Open_HFlipped_VFlipped_Jap
JP10: TRS80_Model_I_Jumper_3_Jap; TRS80_Model_I_Jumper_3_Open_HFlipped_Big_Jap
Z5: 74LS10; TRS80_Model_I_DIP14_Jap
Z7, Z28, Z34, Z35: 74LS93; TRS80_Model_I_DIP14_Jap
Z26: 74LS14; TRS80_Model_I_DIP14_Jap
Z44: 74LS00; TRS80_Model_I_DIP14_Jap
Z45: 74LS02; TRS80_Model_I_DIP14_Jap
Z46: 74LS04; TRS80_Model_I_DIP14_Jap

Connections:
+5V: Z7.5 (VCC), Z28.5 (VCC), Z34.5 (VCC), Z35.5 (VCC)
C1: Z34.9 (Q1)
C2: Z28.14 (CP0), Z34.8 (Q2)
C3: Z28.1 (CP1..3), Z28.12 (Q0)
C4: Z5.10, Z28.9 (Q1)
C5: Z5.11, Z28.8 (Q2)
DOT_CLK: Z34.1 (CP1..3)
GND: Z7.10 (GND), Z28.10 (GND), Z34.2 (R0(1)), Z34.3 (R0(2)), Z34.10 (GND), Z35.10 (GND)
HDRV: Z5.9, Z28.11 (Q3), Z35.14 (CP0)
L0: Z35.1 (CP1..3), Z35.12 (Q0), Z45.2
L1: Z35.9 (Q1)
L2: JP10.1 (A), Z5.3, Z35.8 (Q2)
L3: Z5.5, Z34.14 (CP0), Z35.11 (Q3)
unnamed: JP6.2 (B), Z5.2
unnamed: JP10.2 (B), Z5.4
unnamed: JP10.3 (A), Z46.4
unnamed: Z5.6, Z26.1
unnamed: Z26.2, Z35.2 (R0(1)), Z35.3 (R0(2))
unnamed: Z7.2 (R0(1)), Z7.3 (R0(2)), Z26.10
unnamed: Z5.12, Z26.11
unnamed: Z26.12, Z28.2 (R0(1)), Z28.3 (R0(2))
unnamed: Z5.8, Z26.13
unnamed: Z44.3, Z45.3
unnamed: Z45.1, Z46.3
R0: Z7.14 (CP0), Z34.12 (Q0), Z44.1
R1: Z5.13, Z7.1 (CP1..3), Z7.12 (Q0)
R2: JP6.1 (A), Z7.9 (Q1)
R3: JP6.3 (A), Z7.8 (Q2)
VDRV: Z5.1, Z7.11 (Q3), Z44.2

Notes on the sheet:
Cuts
Jumper
7.92 kHz
660 Hz (650 Hz)
CP0/2
1.98 kHz
NTSC (PAL)
60 Hz (50 Hz)
1.32 kHz (1.30 kHz)
Character line counter
82.5 Hz (81.25 Hz)
27.72 kHz
CP0/11 (CP0/13)
3.96 kHz
110.88 kHz
CP1/4
221.76 kHz
55.44 kHz
15.84 kHz
887.042 kHz
330 Hz (325 Hz)
Column counter
Row counter
NTSC
PAL
CP0/12 (CP0/12 or 13)
443.52 kHz
See Video Sync for more jumpers
CP0/14
165 Hz (162.5 Hz)
Actual Traces
