RetroStack/TRS-80-Model-I-Jap20-E1/KiCAD/VideoGen.kicad_sch

## KiCad design KiCAD/VideoGen.kicad_sch (2025-06-16)

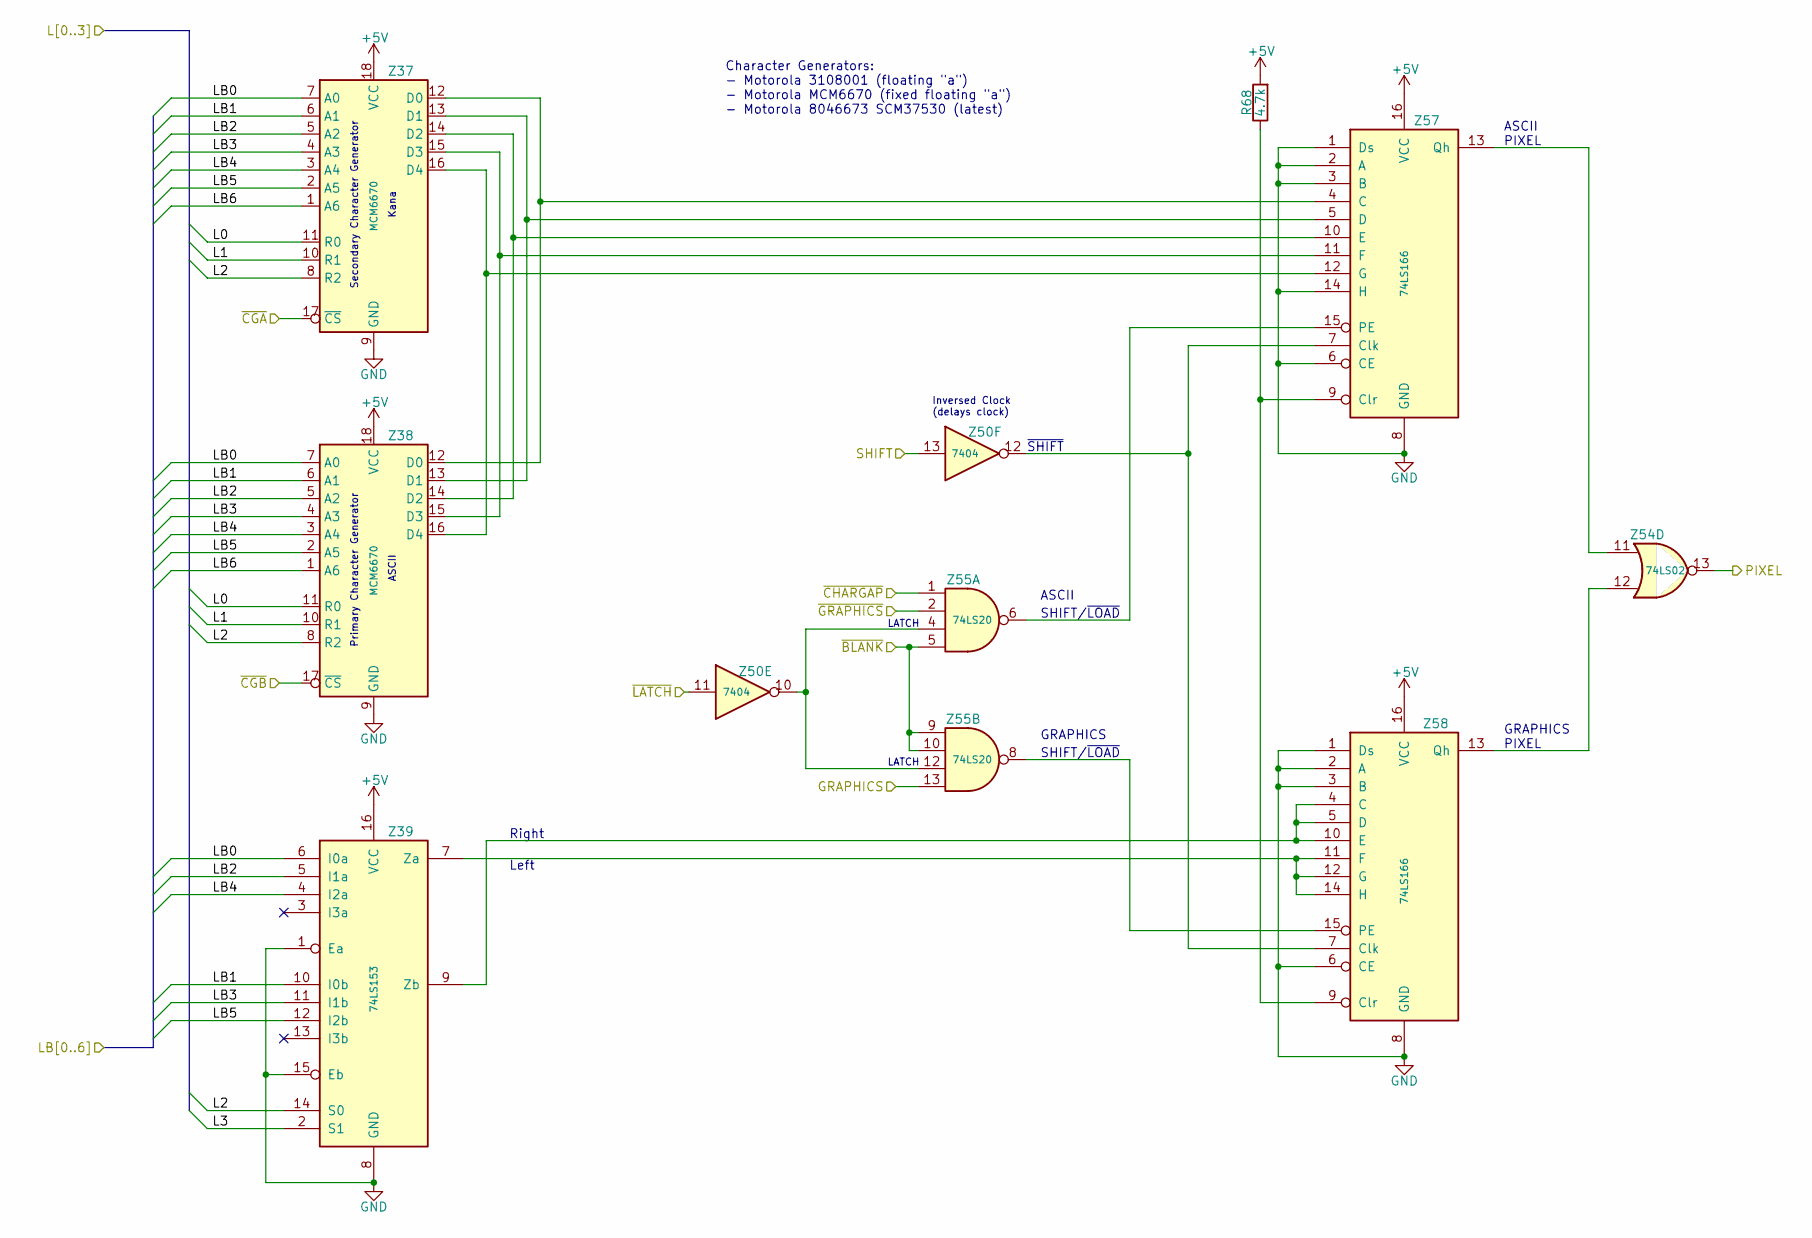
[picture p43: schematic VideoGen.kicad_sch]

Parts:
R68: 4.7k; TRS80_Model_I_R_0.25W_Jap
Z37, Z38: MCM6670; TRS80_Model_I_DIP18_Jap
Z39: 74LS153; TRS80_Model_I_DIP16_Jap
Z50: 7404; TRS80_Model_I_DIP14_Jap
Z54: 74LS02; TRS80_Model_I_DIP14_Jap
Z55: 74LS20; TRS80_Model_I_DIP14_Jap
Z57, Z58: 74LS166; TRS80_Model_I_DIP16_Jap

Connections:
+5V: R68.2, Z37.18 (VCC), Z38.18 (VCC), Z39.16 (VCC), Z57.16 (VCC), Z58.16 (VCC)
GND: Z37.9 (GND), Z38.9 (GND), Z39.1 (Ea), Z39.8 (GND), Z39.15 (Eb), Z57.1 (Ds), Z57.2 (A), Z57.3 (B), Z57.6 (CE), Z57.8 (GND), Z57.14 (H), Z58.1 (Ds), Z58.2 (A), Z58.3 (B), Z58.6 (CE), Z58.8 (GND)
GRAPHICS: Z55.13
L0: Z37.11 (R0), Z38.11 (R0)
L1: Z37.10 (R1), Z38.10 (R1)
L2: Z37.8 (R2), Z38.8 (R2), Z39.14 (S0)
L3: Z39.2 (S1)
LB0: Z37.7 (A0), Z38.7 (A0), Z39.6 (I0a)
LB1: Z37.6 (A1), Z38.6 (A1), Z39.10 (I0b)
LB2: Z37.5 (A2), Z38.5 (A2), Z39.5 (I1a)
LB3: Z37.4 (A3), Z38.4 (A3), Z39.11 (I1b)
LB4: Z37.3 (A4), Z38.3 (A4), Z39.4 (I2a)
LB5: Z37.2 (A5), Z38.2 (A5), Z39.12 (I2b)
LB6: Z37.1 (A6), Z38.1 (A6)
unnamed: R68.1, Z57.9 (Clr), Z58.9 (Clr)
unnamed: Z37.12 (D0), Z38.12 (D0), Z57.4 (C)
unnamed: Z37.13 (D1), Z38.13 (D1), Z57.5 (D)
unnamed: Z37.14 (D2), Z38.14 (D2), Z57.10 (E)
unnamed: Z37.15 (D3), Z38.15 (D3), Z57.11 (F)
unnamed: Z37.16 (D4), Z38.16 (D4), Z57.12 (G)
unnamed: Z39.7 (Za), Z58.11 (F), Z58.12 (G), Z58.14 (H)
unnamed: Z39.9 (Zb), Z58.4 (C), Z58.5 (D), Z58.10 (E)
unnamed: Z50.10, Z55.4, Z55.12
unnamed: Z50.12, Z57.7 (Clk), Z58.7 (Clk)
unnamed: Z54.11, Z57.13 (Qh)
unnamed: Z54.12, Z58.13 (Qh)
unnamed: Z55.6, Z57.15 (PE)
unnamed: Z55.8, Z58.15 (PE)
PIXEL: Z54.13
SHIFT: Z50.13
~BLANK: Z55.5, Z55.9, Z55.10
~CGA: Z37.17 (~CS)
~CGB: Z38.17 (~CS)
~CHARGAP: Z55.1
~GRAPHICS: Z55.2
~LATCH: Z50.11

Notes on the sheet:
LATCH
Primary Character Generator
ASCII
Character Generators: - Motorola 3108001 (floating "a") - Motorola MCM6670 (fixed floating "a") - Motorola 8046673 SCM37530 (latest)
SHIFT/~{LOAD}
Kana
Right
GRAPHICS PIXEL
Left
Secondary Character Generator
GRAPHICS
~{SHIFT}
ASCII PIXEL
Inversed Clock (delays clock)
