RetroStack/TRS-80-Model-I-Jap20-E1/KiCAD/VideoMixer.kicad_sch

## KiCad design KiCAD/VideoMixer.kicad_sch (2025-06-16)

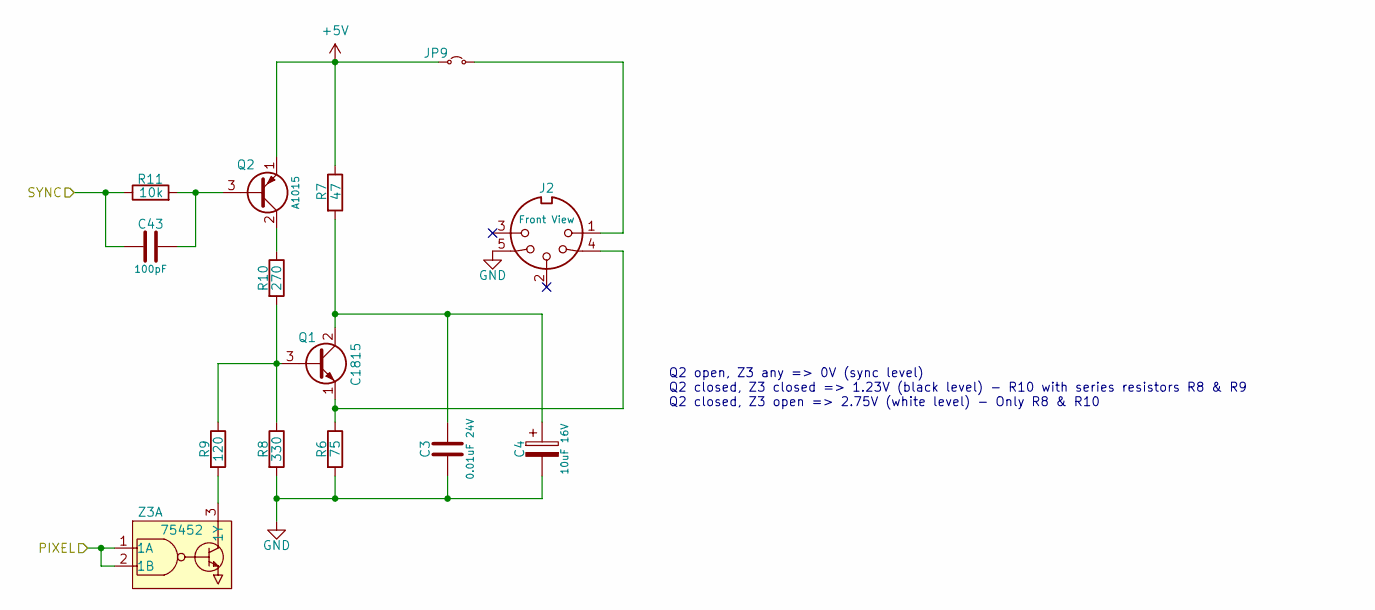
[picture p44: schematic VideoMixer.kicad_sch]

Parts:
C3: 0.01uF 24V; TRS80_Model_I_C_Disc_9.5L_4W_6P_Jap
C4: 10uF 16V; TRS80_Model_I_C_Pol_Radial_5D_2.5P_Jap
C43: 100pF; TRS80_Model_I_C_Disc_9.5L_4W_6P_Small_Jap
J2: Front View; TRS80_Model_I_DIN5_Jap
JP9: TRS80_Model_I_Jumper_2_Jap; TRS80_Model_I_Jumper_2_Open_Jap
Q1: C1815; TRS80_Model_I_Q_Circle_ECB_Jap
Q2: A1015; TRS80_Model_I_Q_Circle_ECB_Jap
R6: 75; TRS80_Model_I_R_0.25W_Jap
R7: 47; TRS80_Model_I_R_0.25W_Jap
R8: 330; TRS80_Model_I_R_0.25W_Jap
R9: 120; TRS80_Model_I_R_0.25W_Jap
R10: 270; TRS80_Model_I_R_0.25W_Jap
R11: 10k; TRS80_Model_I_R_0.25W_Jap
Z3: 75452; TRS80_Model_I_DIP8_Jap

Connections:
+5V: JP9.1 (A), Q2.1 (E), R7.1
GND: C3.2, C4.2, J2.5, R6.2, R8.2
unnamed: C3.1, C4.1, Q1.2 (C), R7.2
unnamed: C43.1, Q2.3 (B), R11.2
unnamed: J2.1, JP9.2 (B)
unnamed: J2.4, Q1.1 (E), R6.1
unnamed: Q1.3 (B), R8.1, R9.1, R10.2
unnamed: Q2.2 (C), R10.1
unnamed: R9.2, Z3.3 (1Y)
PIXEL: Z3.1 (1A), Z3.2 (1B)
SYNC: C43.2, R11.1

Notes on the sheet:
Q2 open, Z3 any => 0V (sync level) Q2 closed, Z3 closed => 1.23V (black level) - R10 with series resistors R8 & R9 Q2 closed, Z3 open => 2.75V (white level) - Only R8 & R10
