RetroStack/TRS-80-Model-I-Jap20-E1/KiCAD/VideoMode.kicad_sch

## KiCad design KiCAD/VideoMode.kicad_sch (2025-06-16)

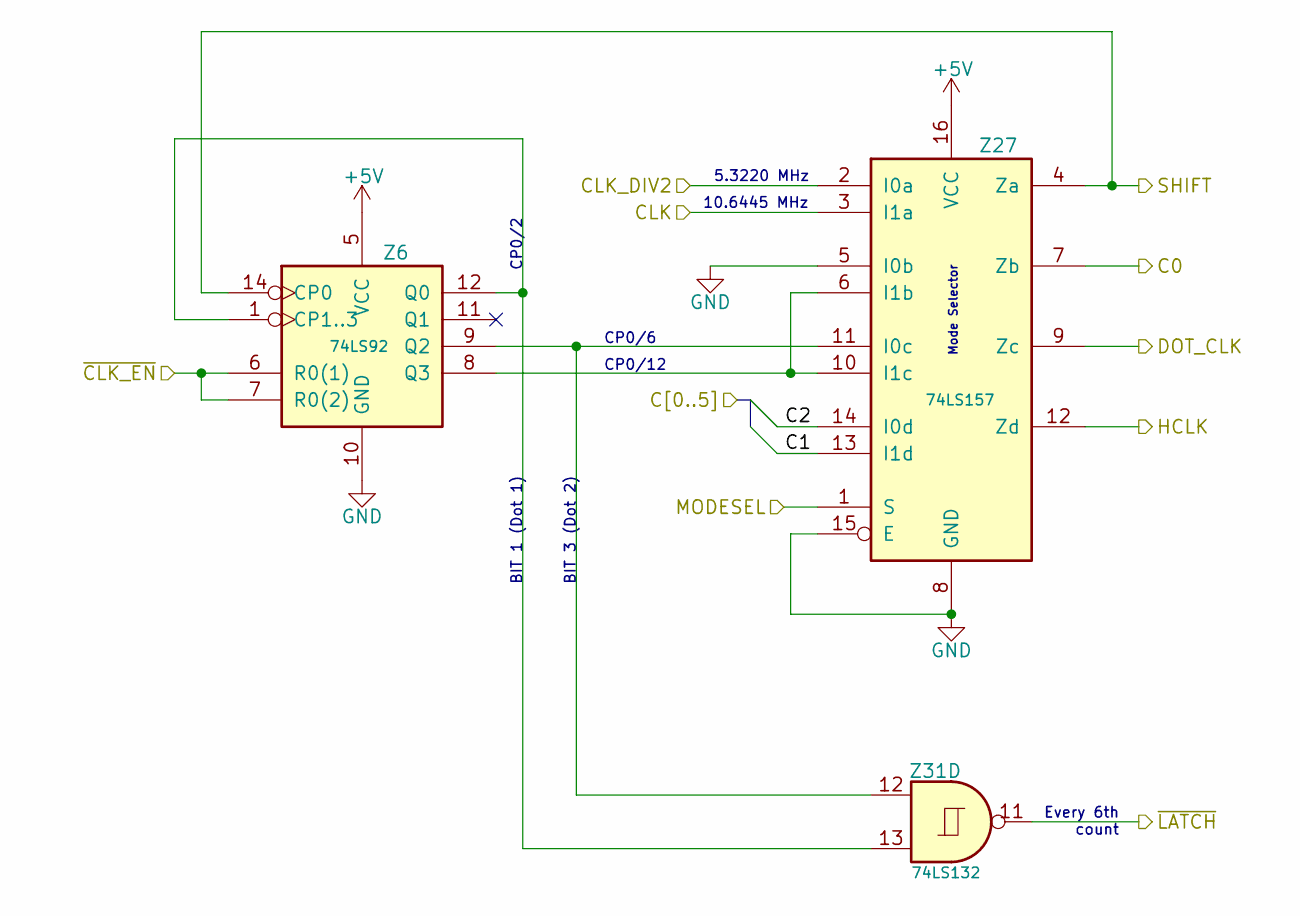
[picture p45: schematic VideoMode.kicad_sch]

Parts:
Z6: 74LS92; TRS80_Model_I_DIP14_Jap
Z27: 74LS157; TRS80_Model_I_DIP16_Jap
Z31: 74LS132; TRS80_Model_I_DIP14_Jap

Connections:
+5V: Z6.5 (VCC), Z27.16 (VCC)
C0: Z27.7 (Zb)
C1: Z27.13 (I1d)
C2: Z27.14 (I0d)
CLK: Z27.3 (I1a)
CLK_DIV2: Z27.2 (I0a)
DOT_CLK: Z27.9 (Zc)
GND: Z6.10 (GND), Z27.5 (I0b), Z27.8 (GND), Z27.15 (E)
HCLK: Z27.12 (Zd)
MODESEL: Z27.1 (S)
unnamed: Z6.8 (Q3), Z27.6 (I1b), Z27.10 (I1c)
unnamed: Z6.9 (Q2), Z27.11 (I0c), Z31.12
unnamed: Z6.1 (CP1..3), Z6.12 (Q0), Z31.13
SHIFT: Z6.14 (CP0), Z27.4 (Za)
~CLK_EN: Z6.6 (R0(1)), Z6.7 (R0(2))
~LATCH: Z31.11

Notes on the sheet:
CP0/6
BIT 1 (Dot 1)
CP0/2
BIT 3 (Dot 2)
CP0/12
10.6445 MHz
Every 6th count
Mode Selector
5.3220 MHz
