RetroStack/TRS-80-Model-I-Jap20-E1/KiCAD/VideoRAM.kicad_sch

## KiCad design KiCAD/VideoRAM.kicad_sch (2025-06-16)

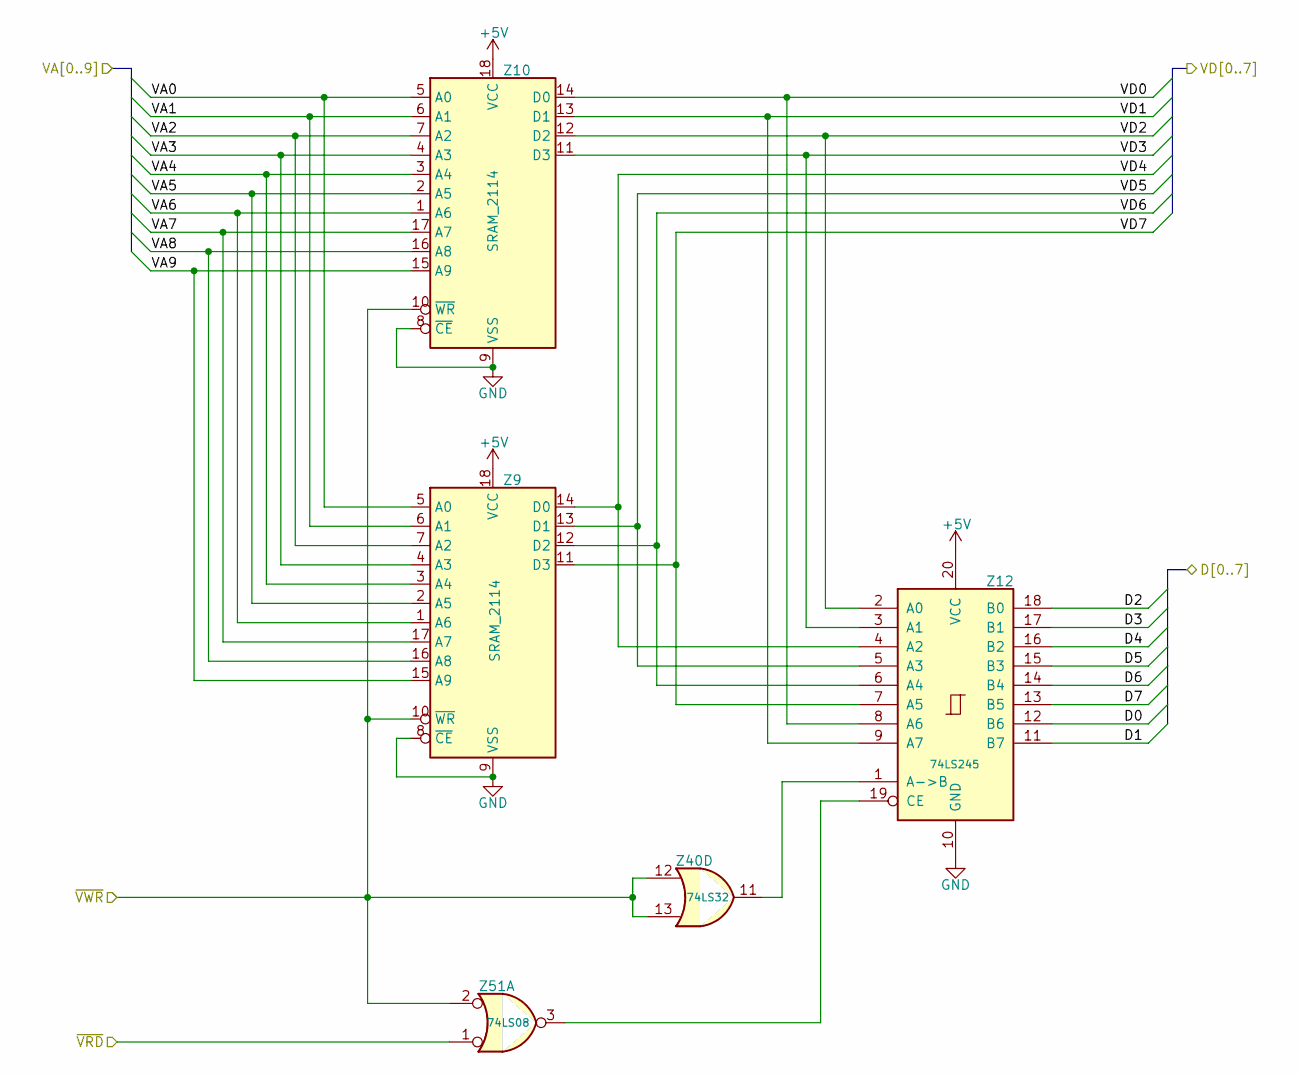
[picture p46: schematic VideoRAM.kicad_sch]

Parts:
Z9, Z10: SRAM_2114; TRS80_Model_I_DIP18_Jap
Z12: 74LS245; TRS80_Model_I_DIP20_Jap
Z40: 74LS32; TRS80_Model_I_DIP14_Jap
Z51: 74LS08; TRS80_Model_I_DIP14_Jap

Connections:
+5V: Z9.18 (VCC), Z10.18 (VCC), Z12.20 (VCC)
D0: Z12.12 (B6)
D1: Z12.11 (B7)
D2: Z12.18 (B0)
D3: Z12.17 (B1)
D4: Z12.16 (B2)
D5: Z12.15 (B3)
D6: Z12.14 (B4)
D7: Z12.13 (B5)
GND: Z9.8 (~CE), Z9.9 (VSS), Z10.8 (~CE), Z10.9 (VSS), Z12.10 (GND)
unnamed: Z12.1 (A->B), Z40.11
unnamed: Z12.19 (CE), Z51.3
VA0: Z9.5 (A0), Z10.5 (A0)
VA1: Z9.6 (A1), Z10.6 (A1)
VA2: Z9.7 (A2), Z10.7 (A2)
VA3: Z9.4 (A3), Z10.4 (A3)
VA4: Z9.3 (A4), Z10.3 (A4)
VA5: Z9.2 (A5), Z10.2 (A5)
VA6: Z9.1 (A6), Z10.1 (A6)
VA7: Z9.17 (A7), Z10.17 (A7)
VA8: Z9.16 (A8), Z10.16 (A8)
VA9: Z9.15 (A9), Z10.15 (A9)
VD0: Z10.14 (D0), Z12.8 (A6)
VD1: Z10.13 (D1), Z12.9 (A7)
VD2: Z10.12 (D2), Z12.2 (A0)
VD3: Z10.11 (D3), Z12.3 (A1)
VD4: Z9.14 (D0), Z12.4 (A2)
VD5: Z9.13 (D1), Z12.5 (A3)
VD6: Z9.12 (D2), Z12.6 (A4)
VD7: Z9.11 (D3), Z12.7 (A5)
~VRD: Z51.1
~VWR: Z9.10 (~WR), Z10.10 (~WR), Z40.12, Z40.13, Z51.2
