RetroStack/TRS-80-Model-I-Jap20-E1/KiCAD/VideoSync.kicad_sch

## KiCad design KiCAD/VideoSync.kicad_sch (2025-06-16)

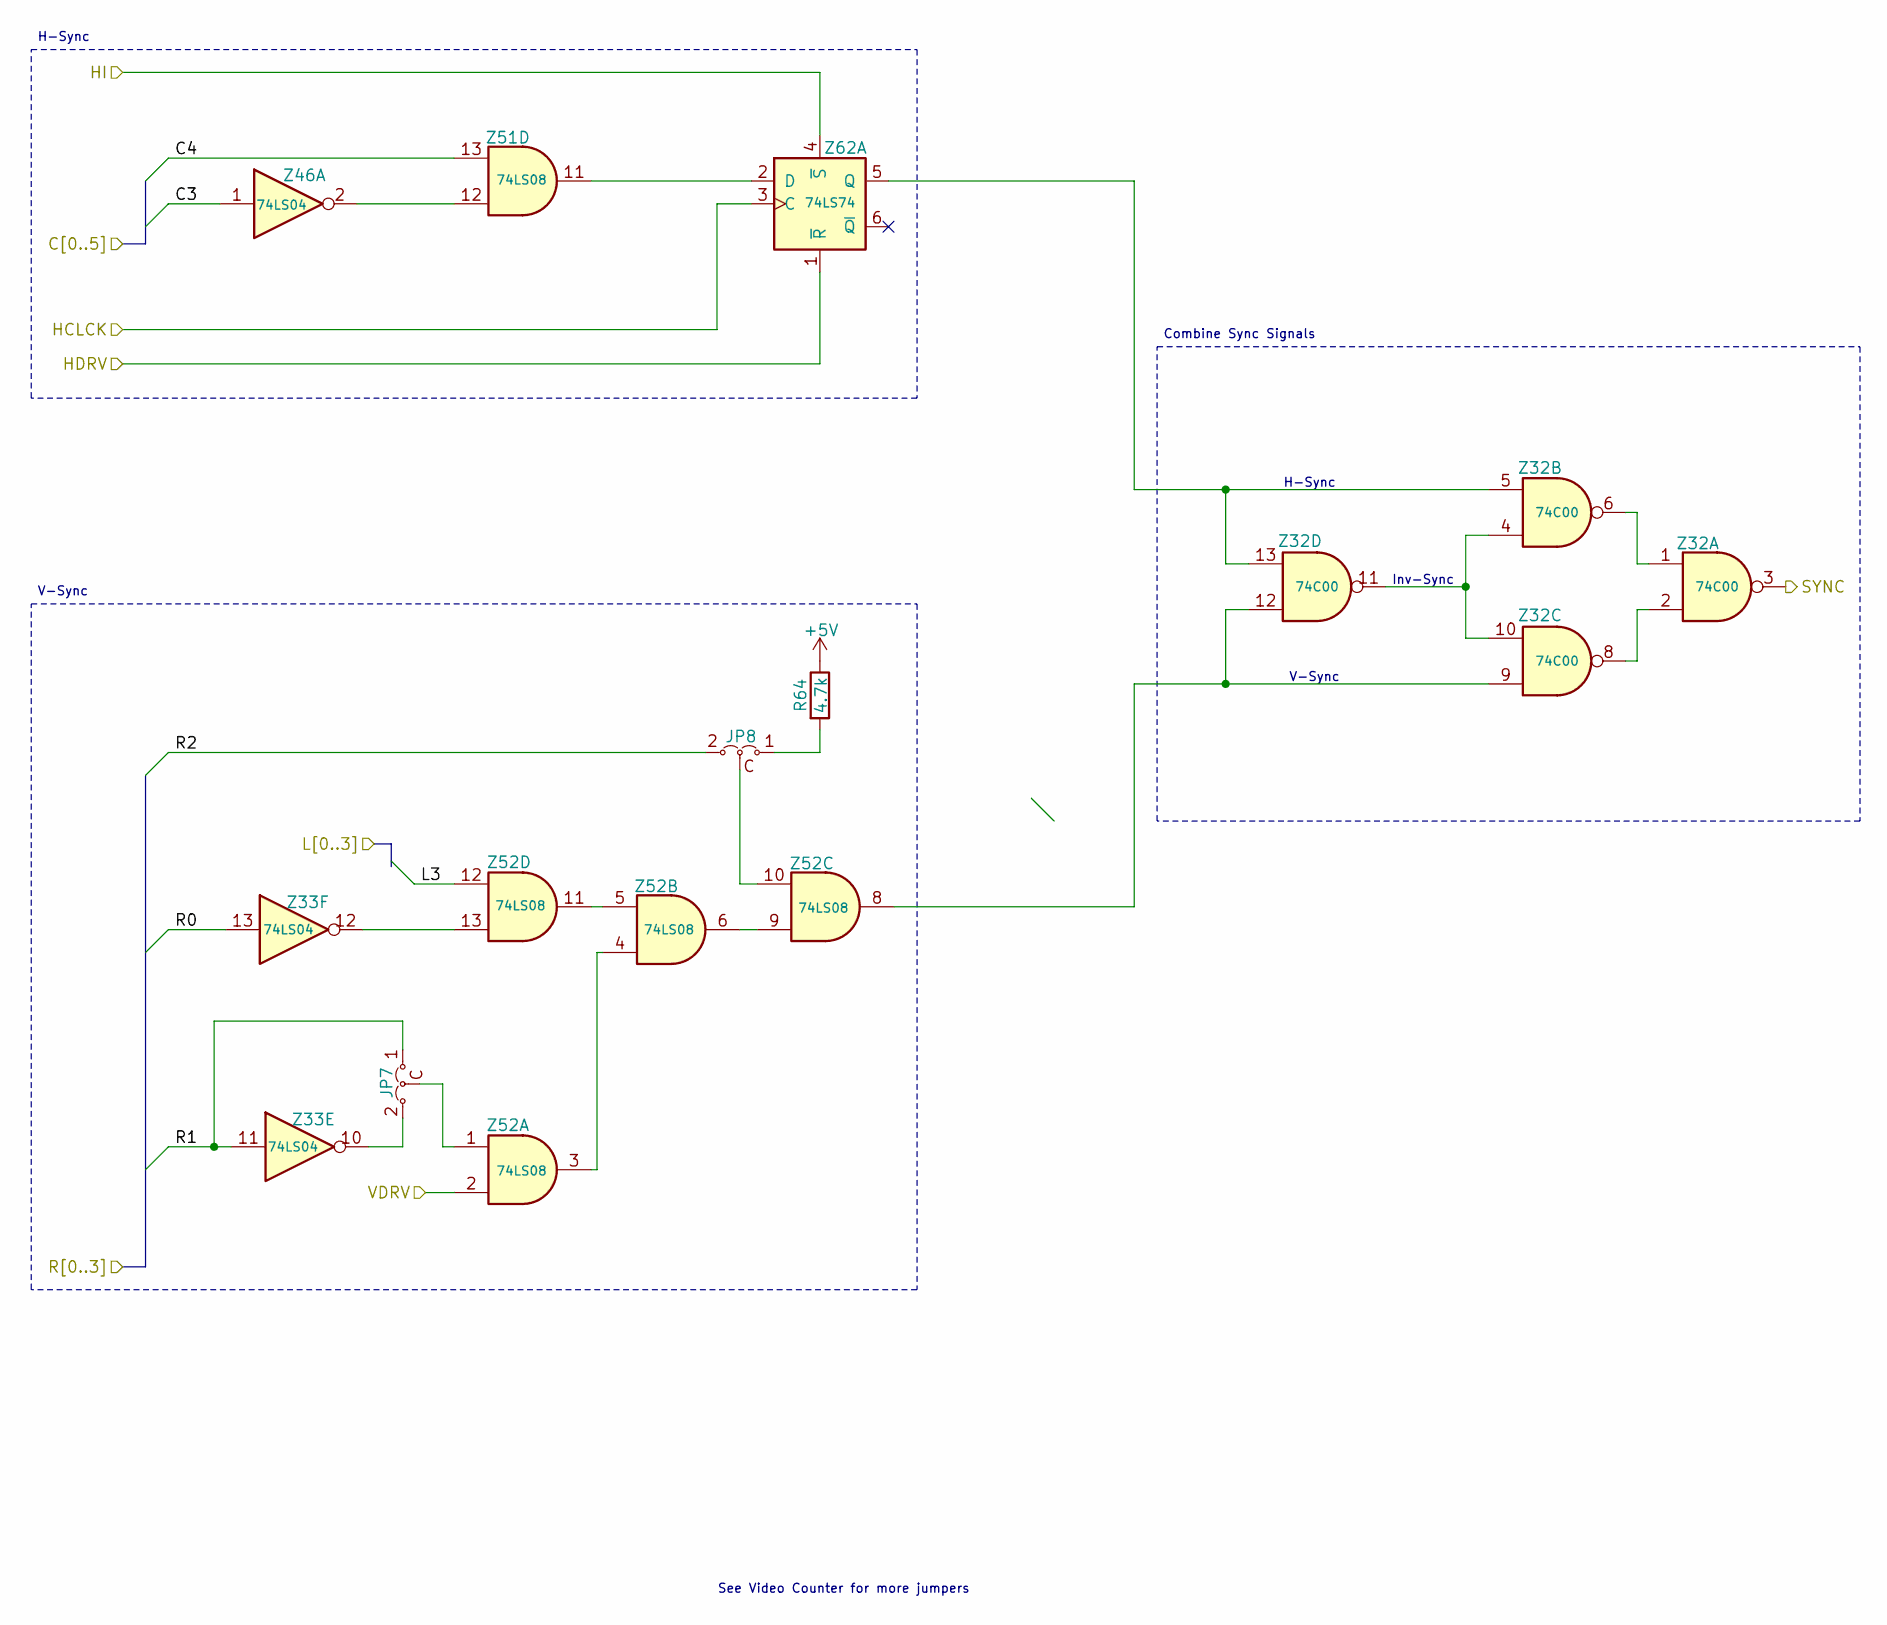
[picture p47: schematic VideoSync.kicad_sch]

Parts:
JP7: TRS80_Model_I_Jumper_3_Jap; TRS80_Model_I_Jumper_3_Open_HFlipped_VFlipped_Jap
JP8: TRS80_Model_I_Jumper_3_Jap; TRS80_Model_I_Jumper_3_Open_Jap
R64: 4.7k; TRS80_Model_I_R_0.25W_Jap
Z32: 74C00; TRS80_Model_I_DIP14_Jap
Z33, Z46: 74LS04; TRS80_Model_I_DIP14_Jap
Z51, Z52: 74LS08; TRS80_Model_I_DIP14_Jap
Z62: 74LS74; TRS80_Model_I_DIP14_Jap

Connections:
+5V: R64.1
C3: Z46.1
C4: Z51.13
HCLCK: Z62.3 (C)
HDRV: Z62.1 (~R)
HI: Z62.4 (~S)
L3: Z52.12
unnamed: JP7.2 (B), Z52.1
unnamed: JP7.3 (A), Z33.10
unnamed: JP8.1 (A), R64.2
unnamed: JP8.2 (B), Z52.10
unnamed: Z32.1, Z32.6
unnamed: Z32.2, Z32.8
unnamed: Z32.4, Z32.10, Z32.11
unnamed: Z32.9, Z32.12, Z52.8
unnamed: Z32.5, Z32.13, Z62.5 (Q)
unnamed: Z33.12, Z52.13
unnamed: Z46.2, Z51.12
unnamed: Z51.11, Z62.2 (D)
unnamed: Z52.3, Z52.4
unnamed: Z52.6, Z52.9
unnamed: Z52.5, Z52.11
R0: Z33.13
R1: JP7.1 (A), Z33.11
R2: JP8.3 (A)
SYNC: Z32.3
VDRV: Z52.2

Notes on the sheet:
H-Sync
V-Sync
Inv-Sync
Combine Sync Signals
See Video Counter for more jumpers
